Wierdwizard2587/ElectricGuitarMK1/Progress Photos/Design Phase/IMG_8852.JPEG

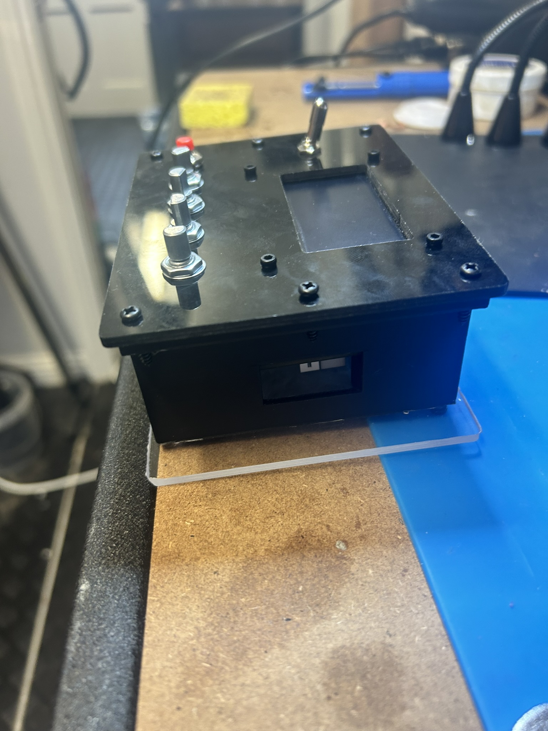
Progress Photos/Design Phase/IMG_8852.JPEG
