Wierdwizard2587/ElectricGuitarMK1/Progress Photos/Design Phase/IMG_9136.JPEG

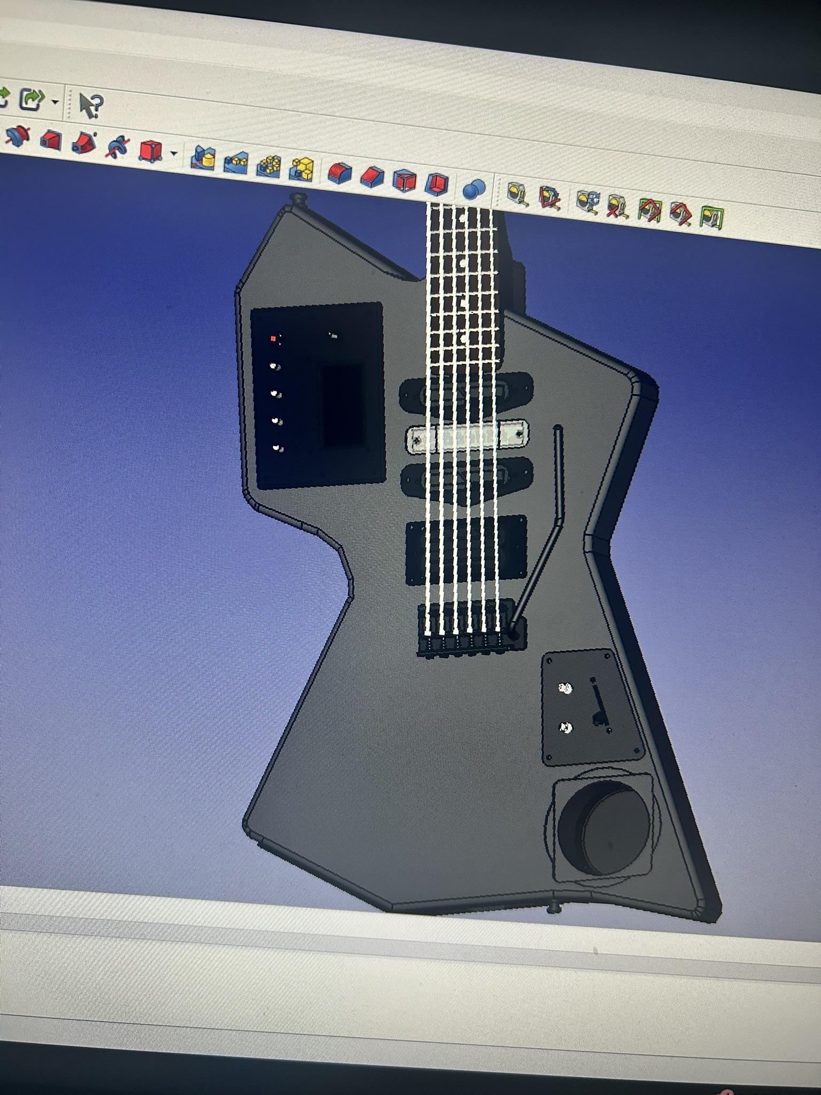
Progress Photos/Design Phase/IMG_9136.JPEG
