Wierdwizard2587/ElectricGuitarMK1/Progress Photos/Design Phase/IMG_9137.JPEG

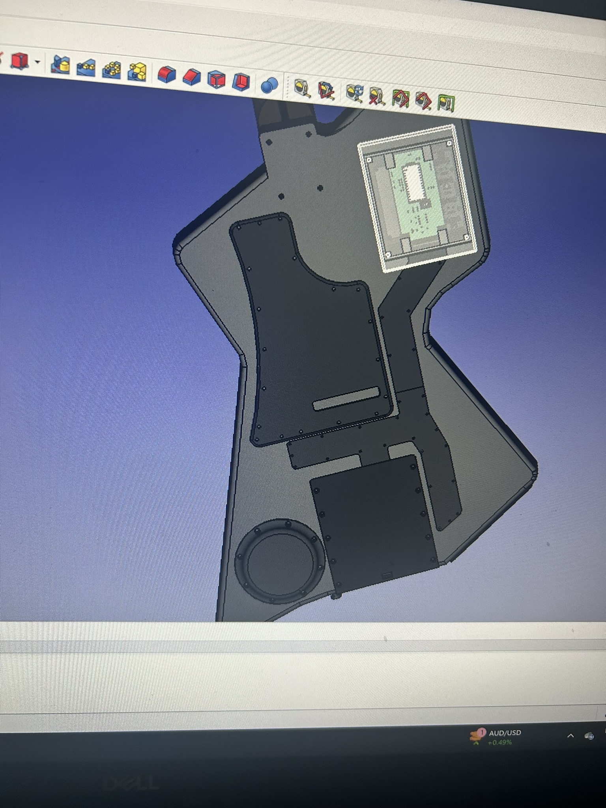
Progress Photos/Design Phase/IMG_9137.JPEG
