Wierdwizard2587/ElectricGuitarMK1/Progress Photos/Embedded Electronics/IMG_9527.jpg

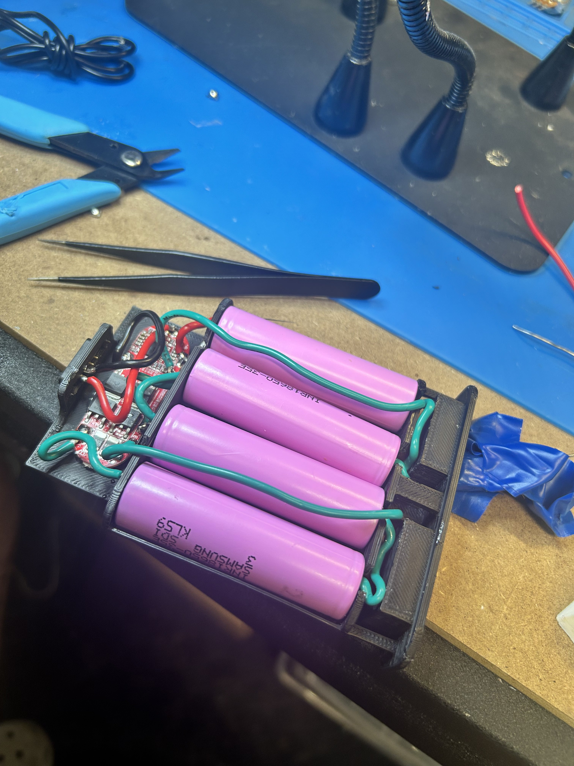
Progress Photos/Embedded Electronics/IMG_9527.jpg
