Wierdwizard2587/ElectricGuitarMK1/Progress Photos/Finished Product/IMG_9553.JPEG

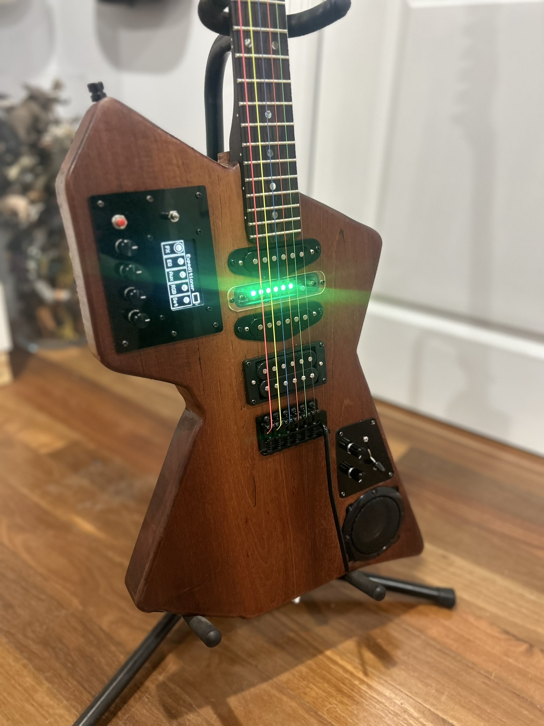
Progress Photos/Finished Product/IMG_9553.JPEG
