Wierdwizard2587/ElectricGuitarMK1/Progress Photos/Finished Product/IMG_9555.JPEG

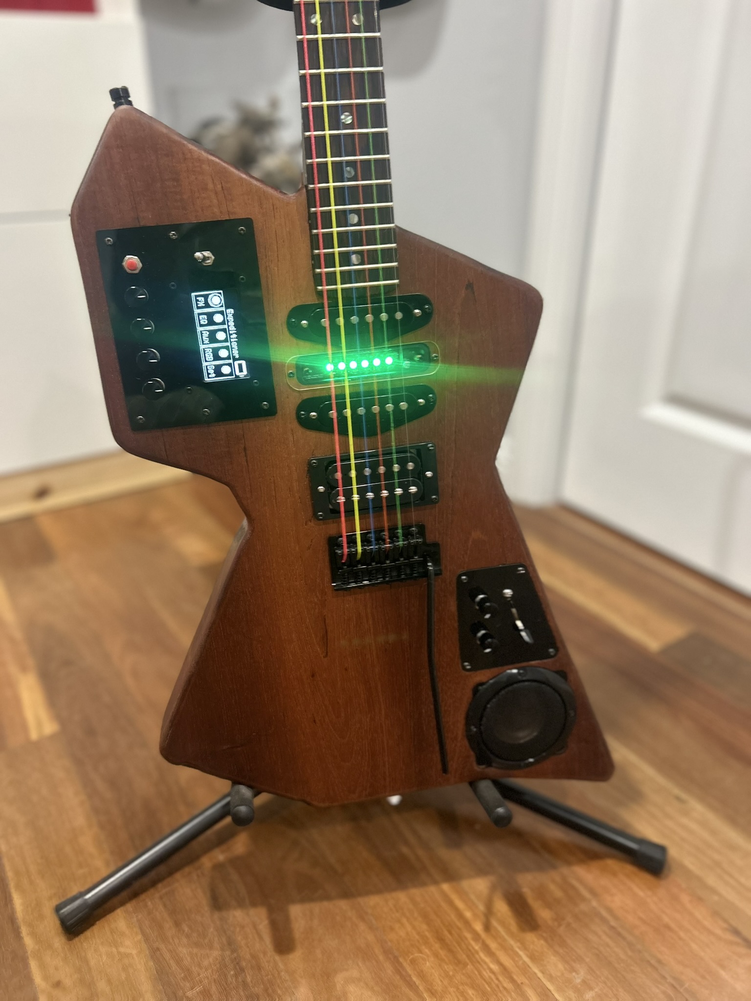
Progress Photos/Finished Product/IMG_9555.JPEG
