Wierdwizard2587/ElectricGuitarMK1/Progress Photos/Finished Product/IMG_9557.JPEG

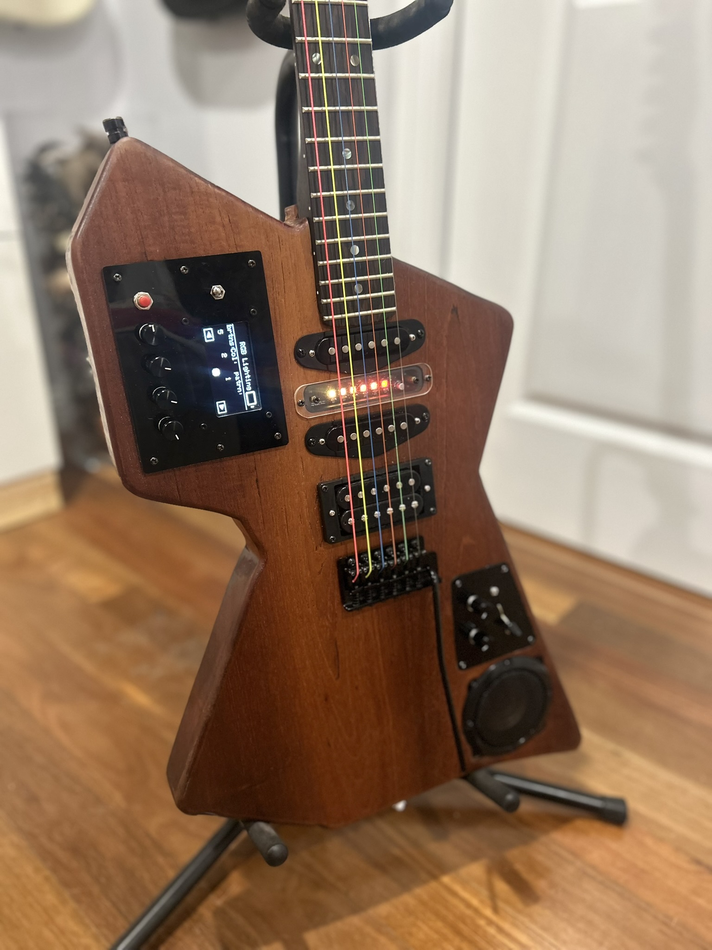
Progress Photos/Finished Product/IMG_9557.JPEG
