Wierdwizard2587/ElectricGuitarMK1/Progress Photos/MK 0 attempt/IMG_7361.JPEG

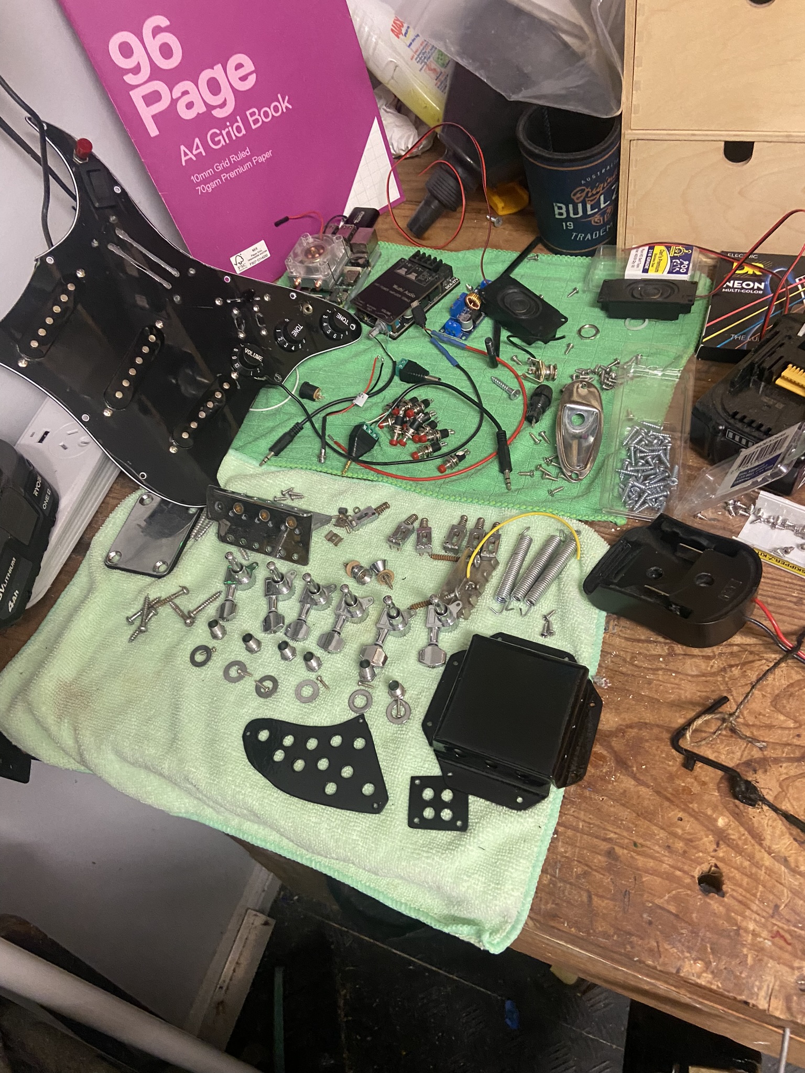
Progress Photos/MK 0 attempt/IMG_7361.JPEG
