Wierdwizard2587/ElectricGuitarMK1/Progress Photos/MK 0 attempt/IMG_7546.JPEG

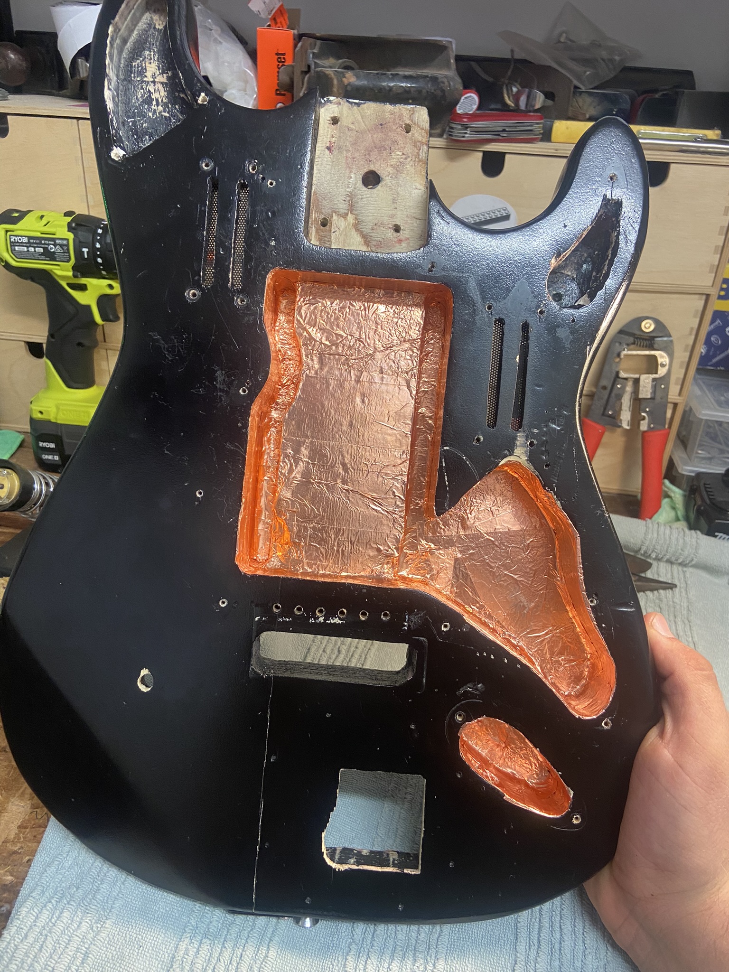
Progress Photos/MK 0 attempt/IMG_7546.JPEG
