Wierdwizard2587/ElectricGuitarMK1/Progress Photos/Skills Learnt/IMG_7960.JPEG

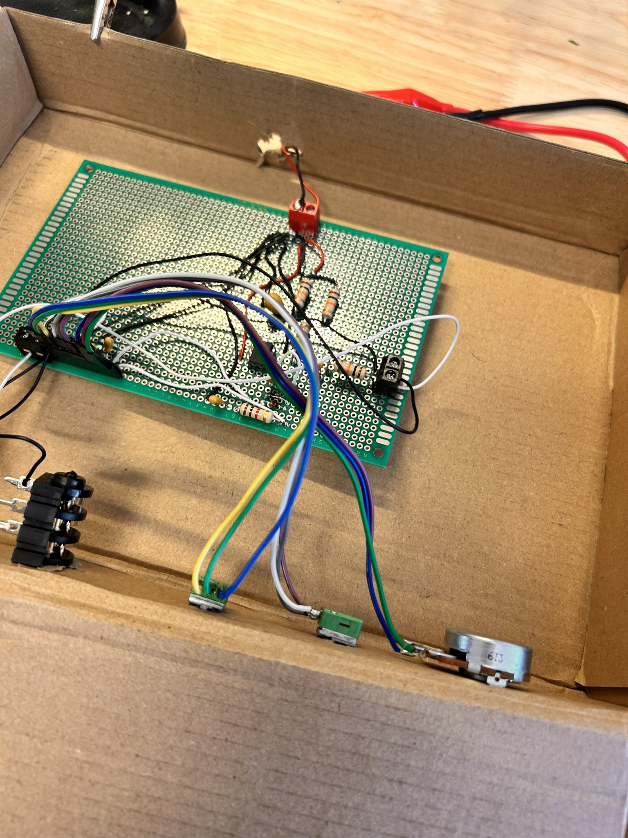
Progress Photos/Skills Learnt/IMG_7960.JPEG
