Wierdwizard2587/ElectricGuitarMK1/Progress Photos/Skills Learnt/IMG_7990.JPEG

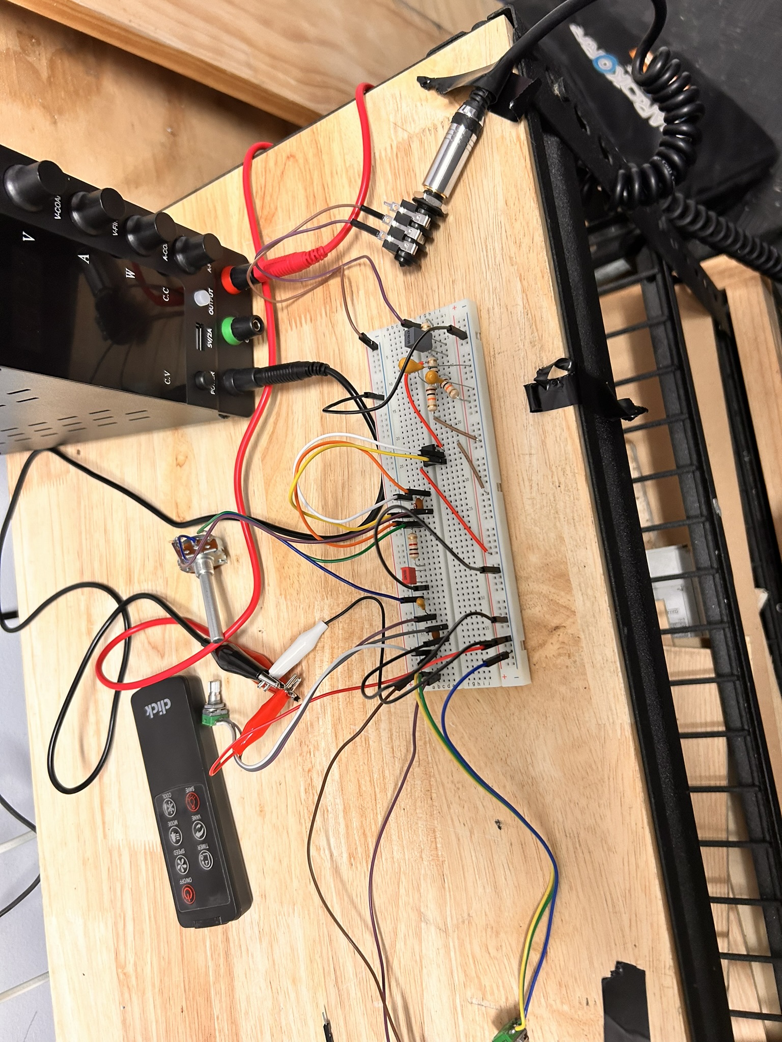
Progress Photos/Skills Learnt/IMG_7990.JPEG
