Wierdwizard2587/ElectricGuitarMK1/Progress Photos/Skills Learnt/IMG_8116.JPEG

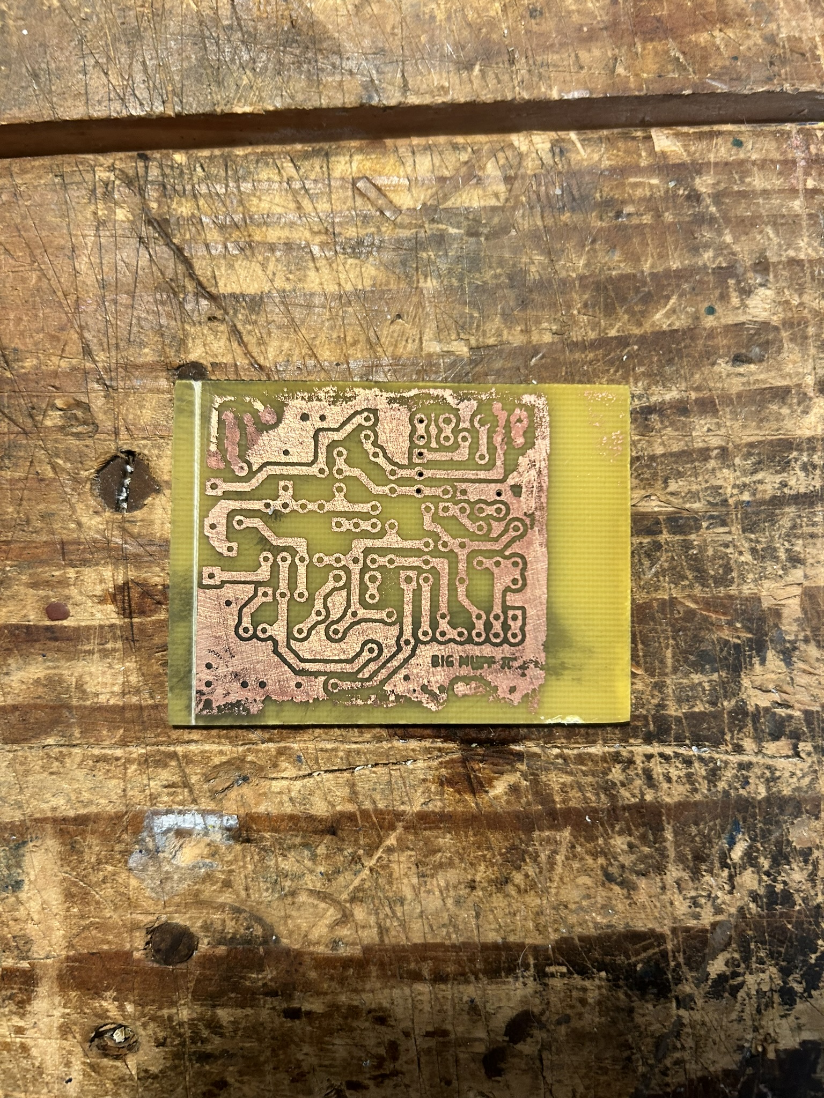
Progress Photos/Skills Learnt/IMG_8116.JPEG
