Wierdwizard2587/ElectricGuitarMK1/Progress Photos/Skills Learnt/IMG_8142.JPEG

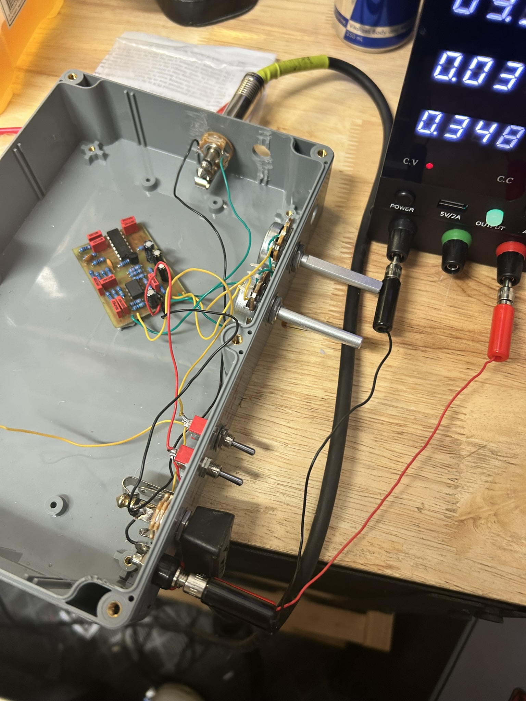
Progress Photos/Skills Learnt/IMG_8142.JPEG
