Wierdwizard2587/ElectricGuitarMK1/Progress Photos/Skills Learnt/IMG_8186.JPEG

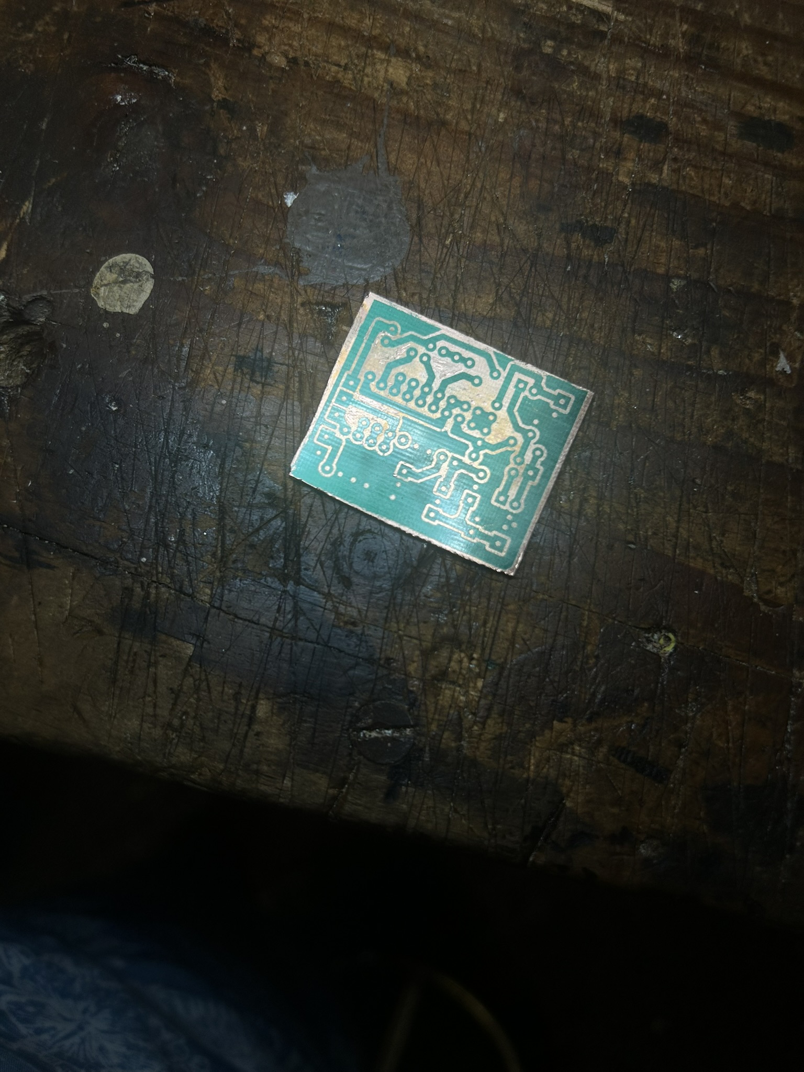
Progress Photos/Skills Learnt/IMG_8186.JPEG
