Wierdwizard2587/ElectricGuitarMK1/Progress Photos/Woodworking/IMG_9257.JPEG

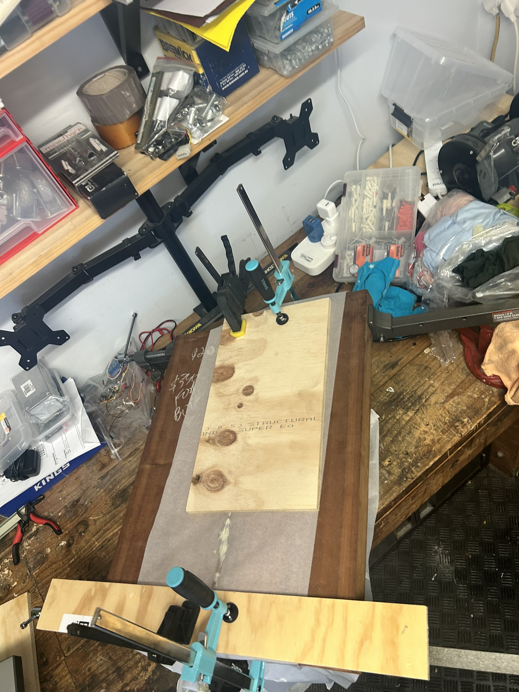
Progress Photos/Woodworking/IMG_9257.JPEG
