Wierdwizard2587/ElectricGuitarMK1/Progress Photos/Woodworking/IMG_9268.JPEG

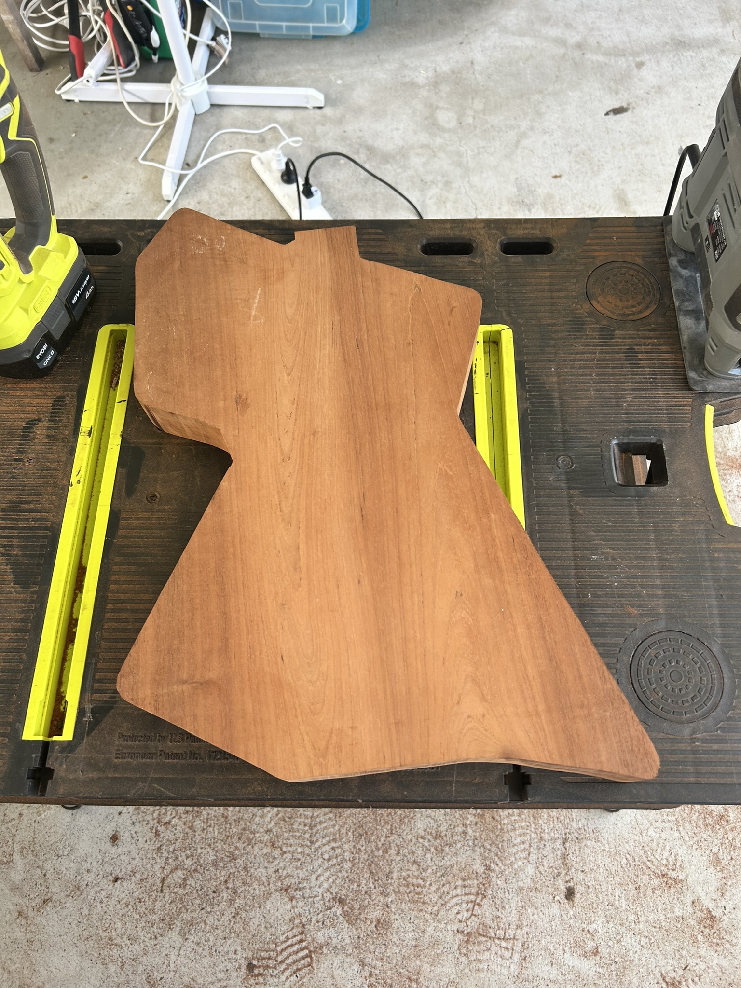
Progress Photos/Woodworking/IMG_9268.JPEG
