Wierdwizard2587/ElectricGuitarMK1/Progress Photos/Woodworking/IMG_9292.JPEG

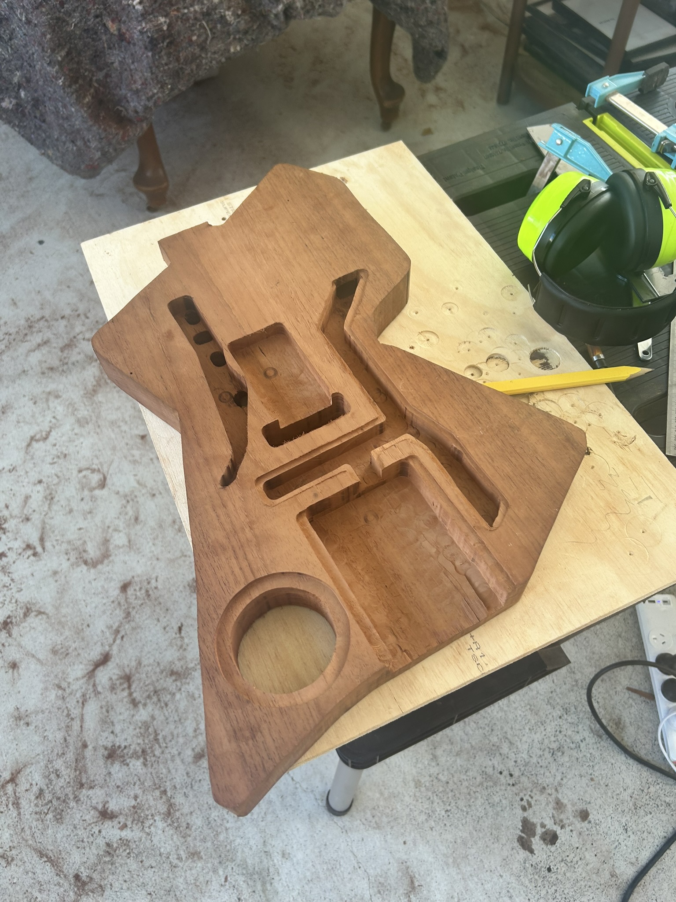
Progress Photos/Woodworking/IMG_9292.JPEG
