Wierdwizard2587/ElectricGuitarMK1/Progress Photos/Woodworking/IMG_9326.JPEG

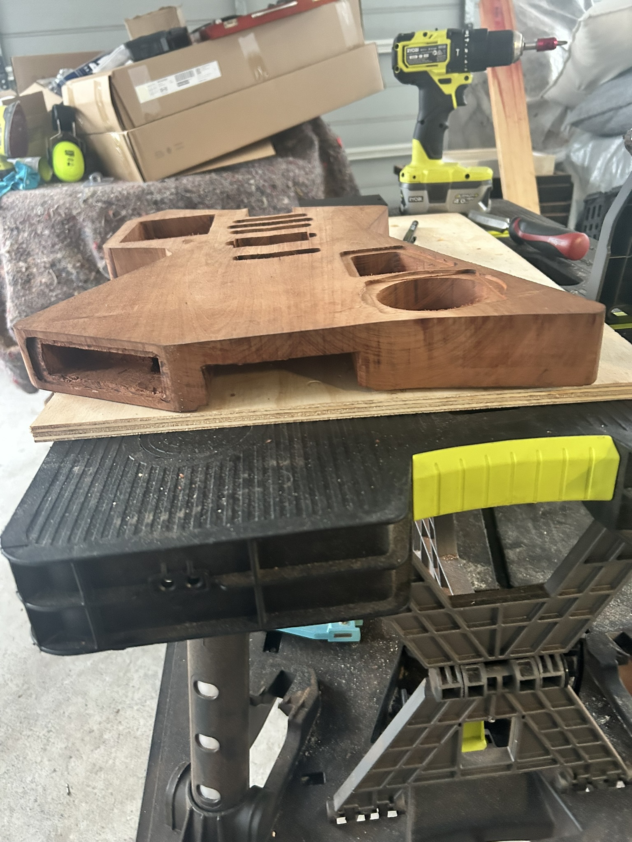
Progress Photos/Woodworking/IMG_9326.JPEG
