Wierdwizard2587/ElectricGuitarMK1/Progress Photos/Woodworking/IMG_9331.JPEG

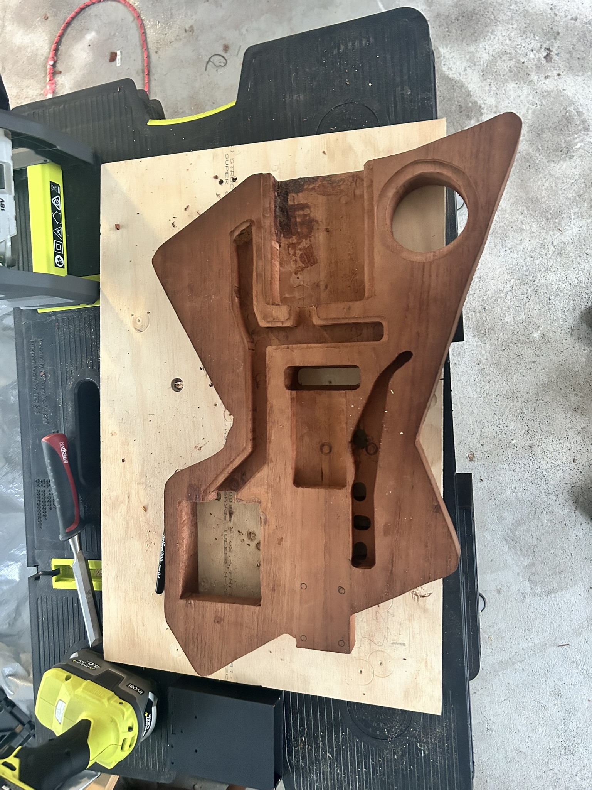
Progress Photos/Woodworking/IMG_9331.JPEG
