Wierdwizard2587/ElectricGuitarMK1/Progress Photos/Woodworking/IMG_9341.JPEG

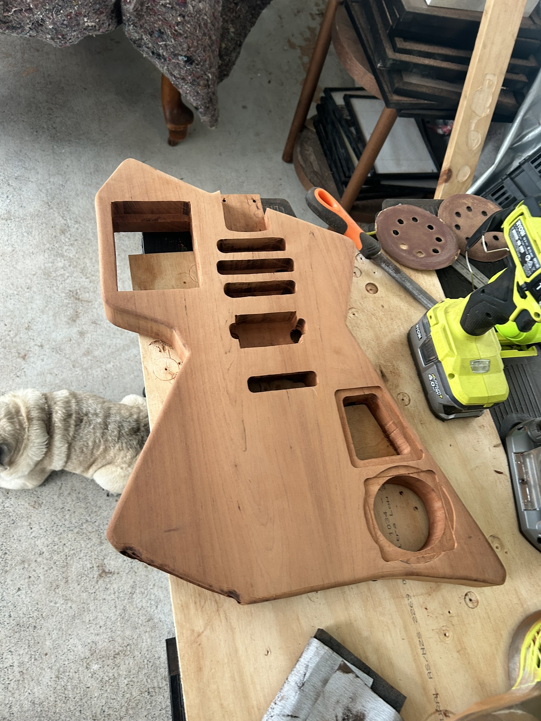
Progress Photos/Woodworking/IMG_9341.JPEG
