Wierdwizard2587/ElectricGuitarMK1/Progress Photos/Woodworking/IMG_9385.JPEG

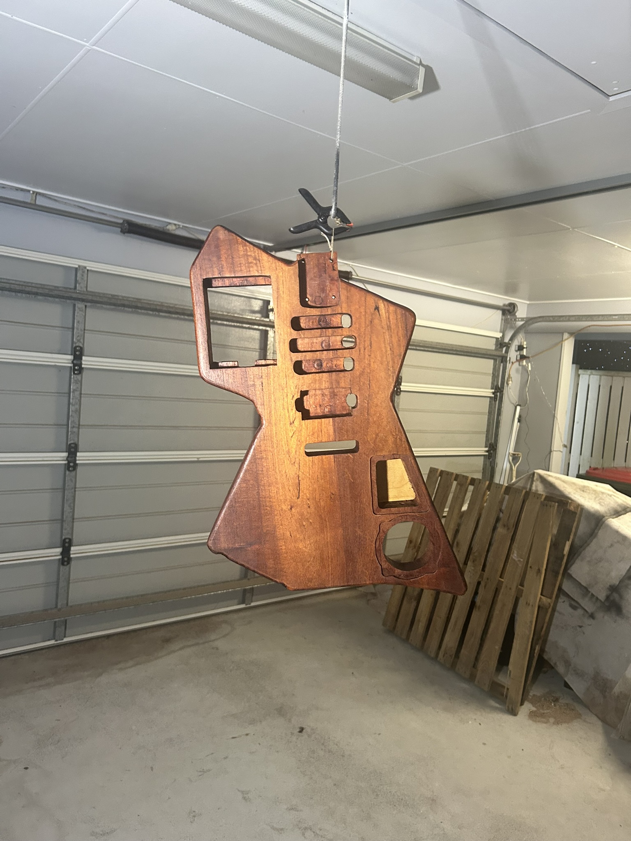
Progress Photos/Woodworking/IMG_9385.JPEG
