Wierdwizard2587/ElectricGuitarMK1/Research and Development/BMS/awg wire chart.webp

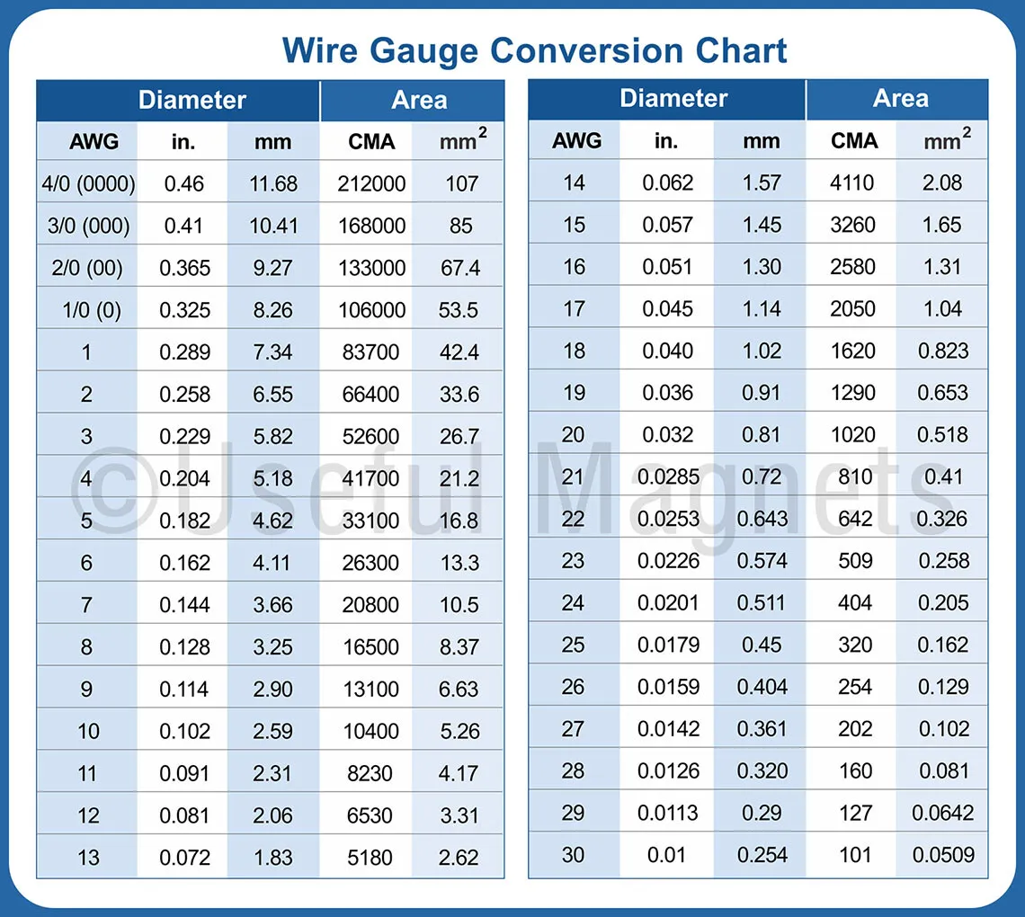
Research and Development/BMS/awg wire chart.webp
