Wierdwizard2587/ElectricGuitarMK1/Research and Development/BMS/Dimensions/Batt-Conn-magnetic-4p-Schem-Sheet.webp

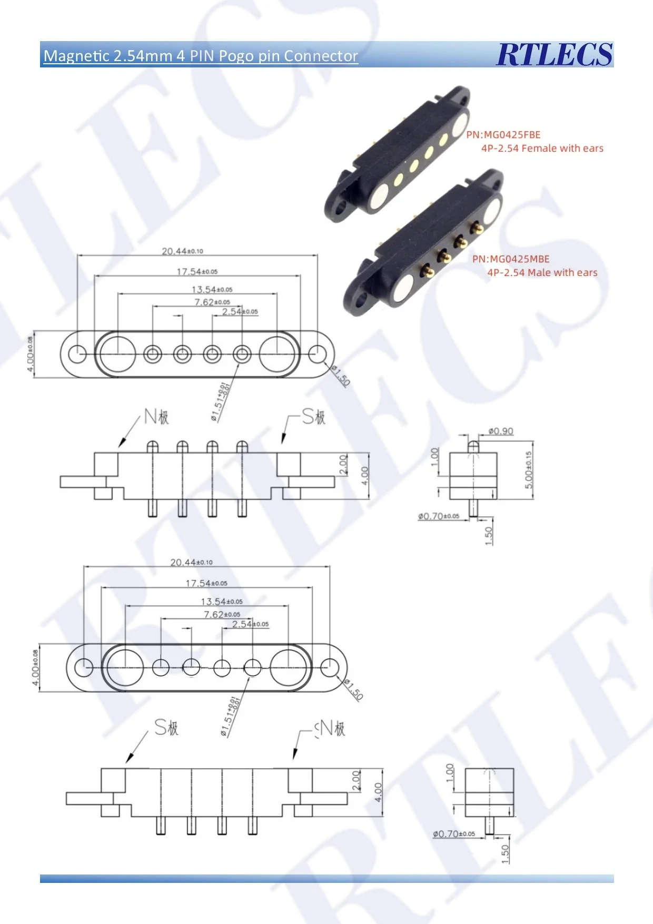
Research and Development/BMS/Dimensions/Batt-Conn-magnetic-4p-Schem-Sheet.webp
