Wierdwizard2587/ElectricGuitarMK1/Research and Development/BMS/Dimensions/battery spring terminal male 4pin dimensions.webp

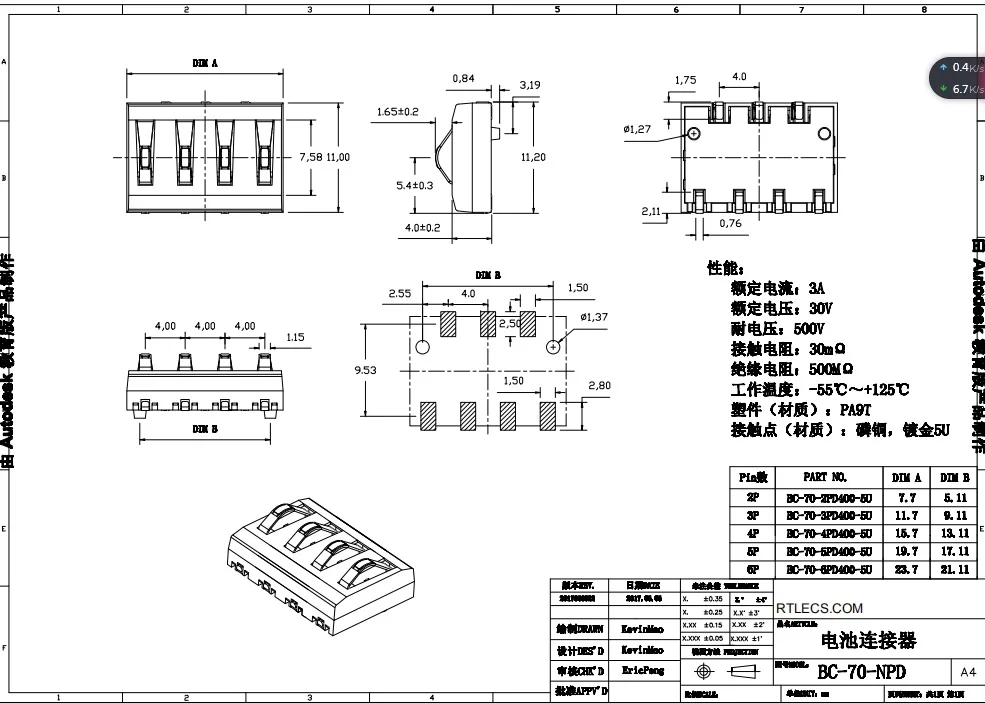
Research and Development/BMS/Dimensions/battery spring terminal male 4pin dimensions.webp
