Wierdwizard2587/ElectricGuitarMK1/Research and Development/BMS/Dimensions/battery terminal femal 4 pin dimensions.webp

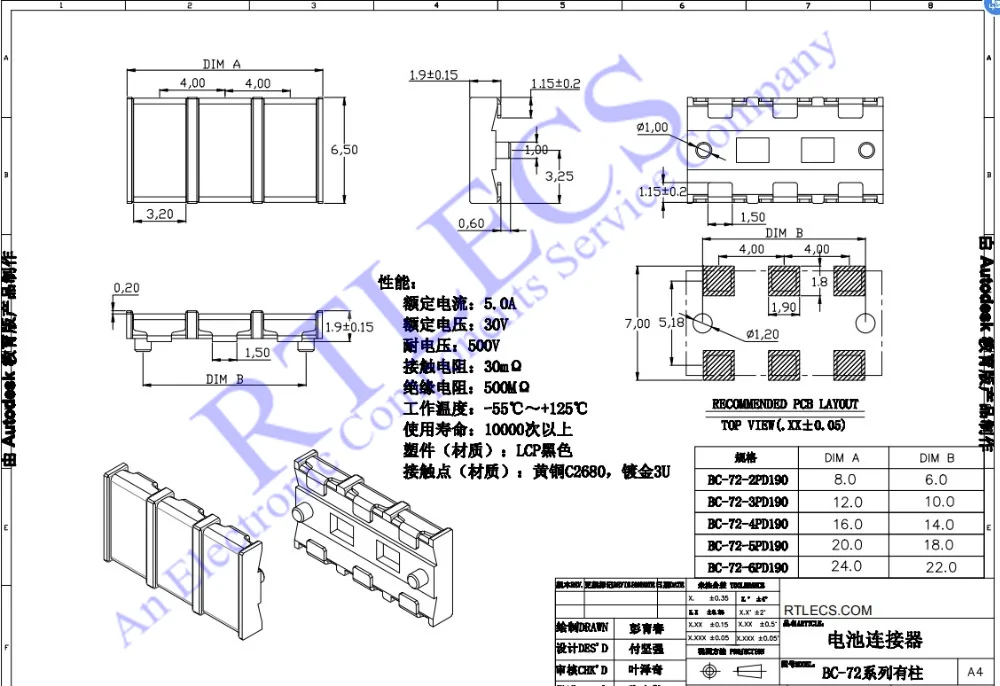
Research and Development/BMS/Dimensions/battery terminal femal 4 pin dimensions.webp
