Wierdwizard2587/ElectricGuitarMK1/Research and Development/BMS/Dimensions/smt battery holders dimensions.png

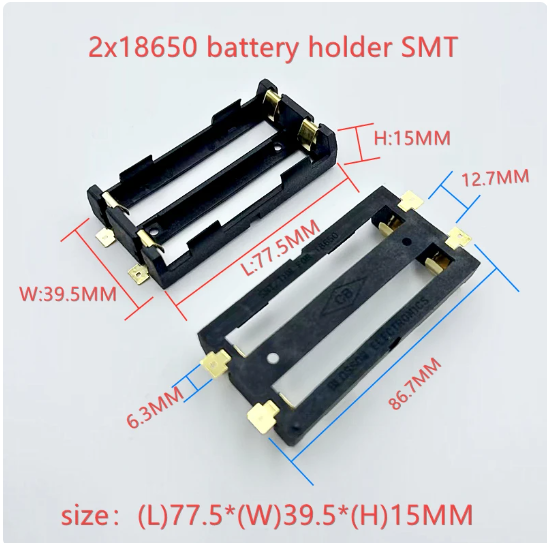
Research and Development/BMS/Dimensions/smt battery holders dimensions.png
