Wierdwizard2587/ElectricGuitarMK1/Research and Development/BMS/Docs/bms board battery and input config .png

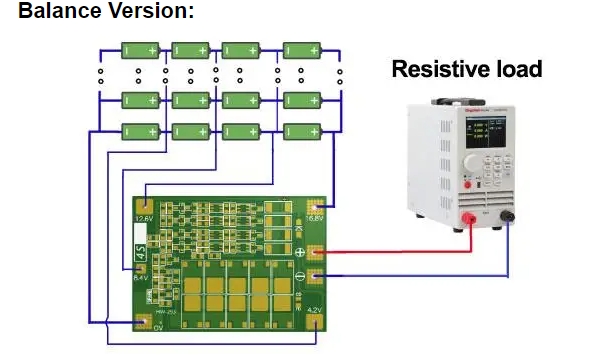
Research and Development/BMS/Docs/bms board battery and input config .png
