Wierdwizard2587/ElectricGuitarMK1/Research and Development/BMS/PCB Design/3.0 BMS/V3.2/bmsboardlayoutv1.png

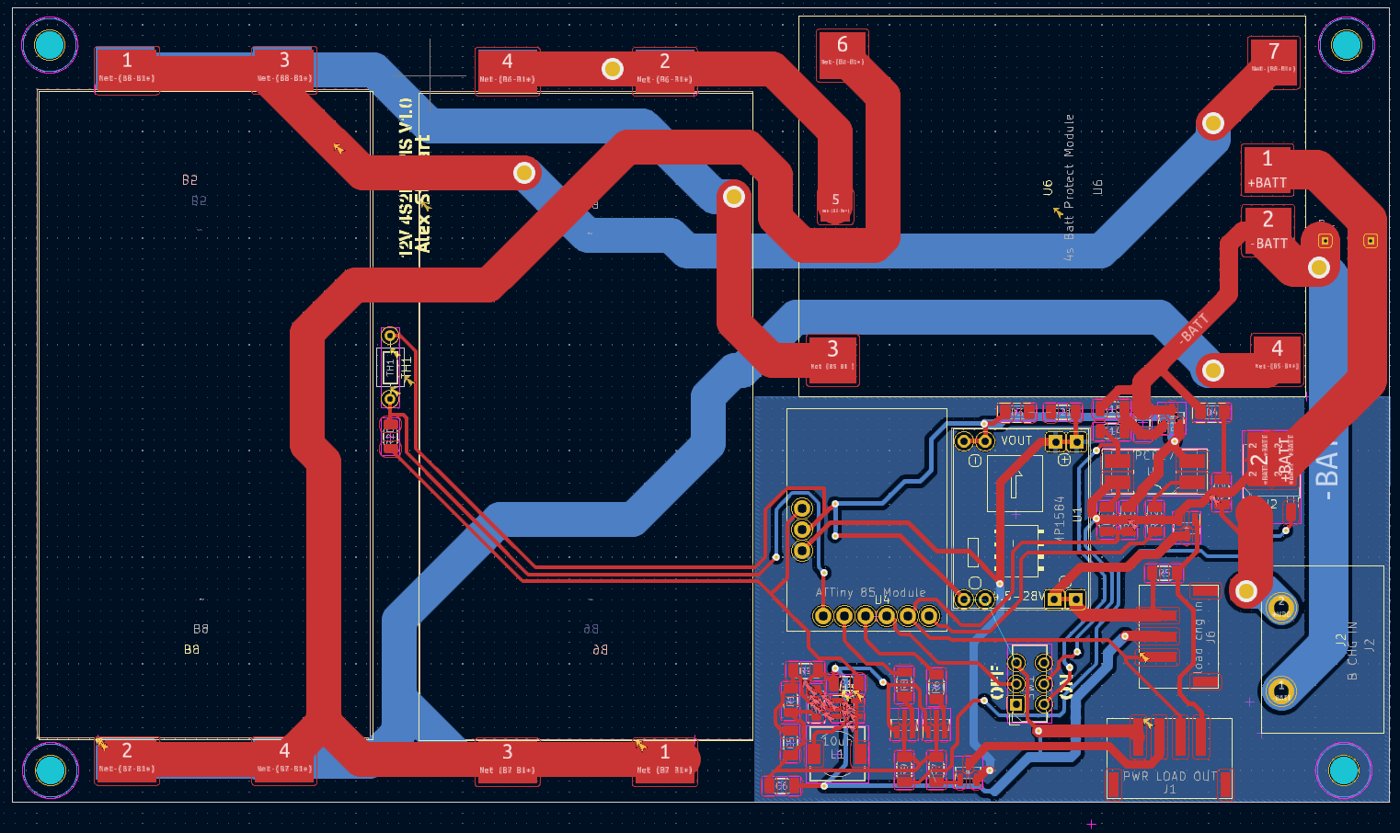
Research and Development/BMS/PCB Design/3.0 BMS/V3.2/bmsboardlayoutv1.png
