Wierdwizard2587/ElectricGuitarMK1/Research and Development/Body design/3d models and docs/spst button/button render.png

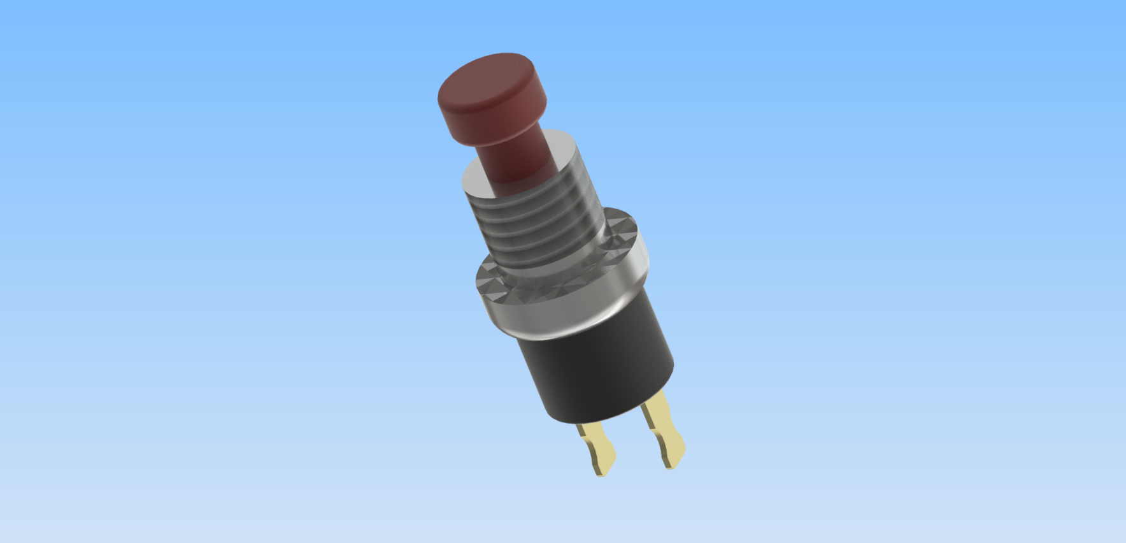
Research and Development/Body design/3d models and docs/spst button/button render.png
