Wierdwizard2587/ElectricGuitarMK1/Research and Development/FX Circuits/ProCo Rat/procoratpcblayout.png

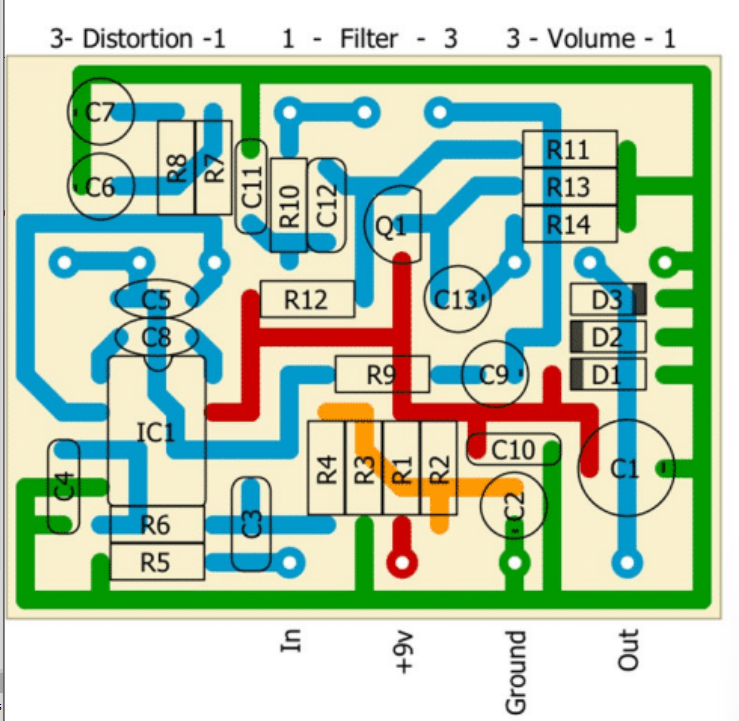
Research and Development/FX Circuits/ProCo Rat/procoratpcblayout.png
