Wierdwizard2587/ElectricGuitarMK1/Research and Development/Interface Section/AFPI/Enclosure Design/3D Models/quad Rotary Encoder Board/Adafruit 5752.png

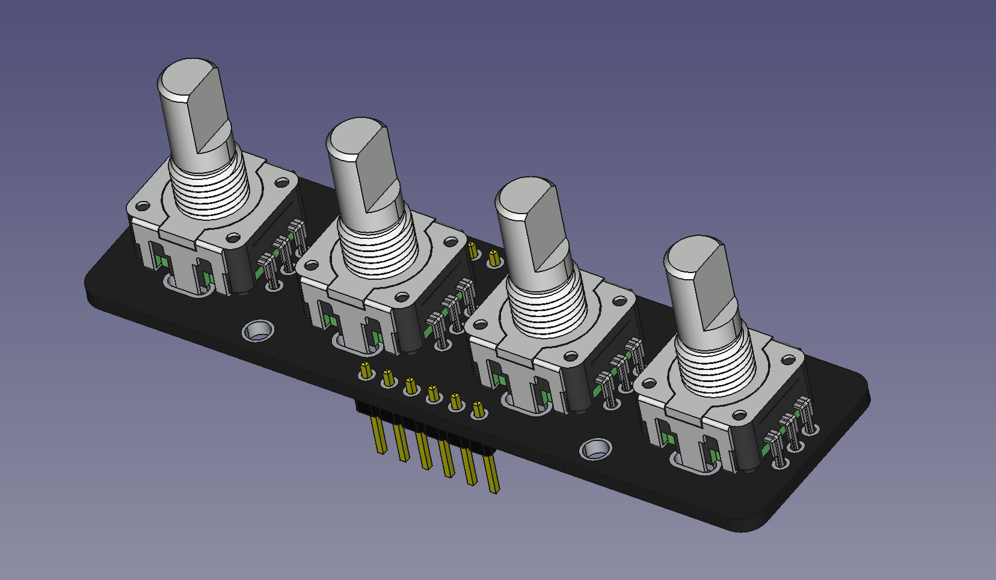
Research and Development/Interface Section/AFPI/Enclosure Design/3D Models/quad Rotary Encoder Board/Adafruit 5752.png
