Wierdwizard2587/ElectricGuitarMK1/Research and Development/Interface Section/AFPI/Enclosure Design/AFPI Final Documents/Enclosure Images/right view.png

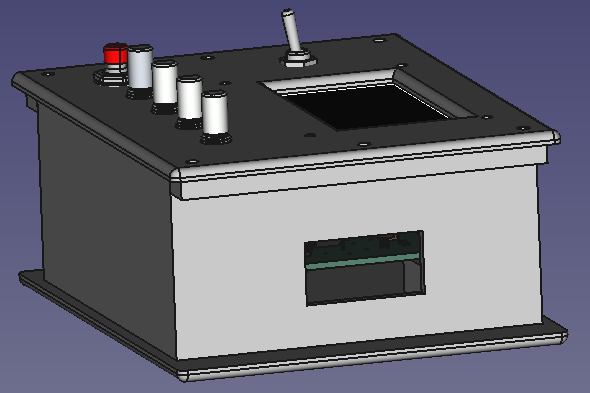
Research and Development/Interface Section/AFPI/Enclosure Design/AFPI Final Documents/Enclosure Images/right view.png
