Wierdwizard2587/ElectricGuitarMK1/Research and Development/Interface Section/compass.jpg

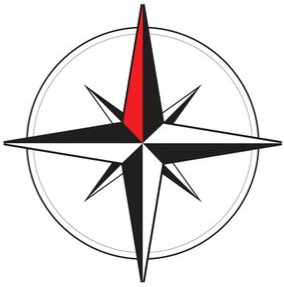
Research and Development/Interface Section/compass.jpg
