Wierdwizard2587/ElectricGuitarMK1/Research and Development/Body design/body and neck scaled 3d models/Expeditioner Model-Body Mk 1.stl

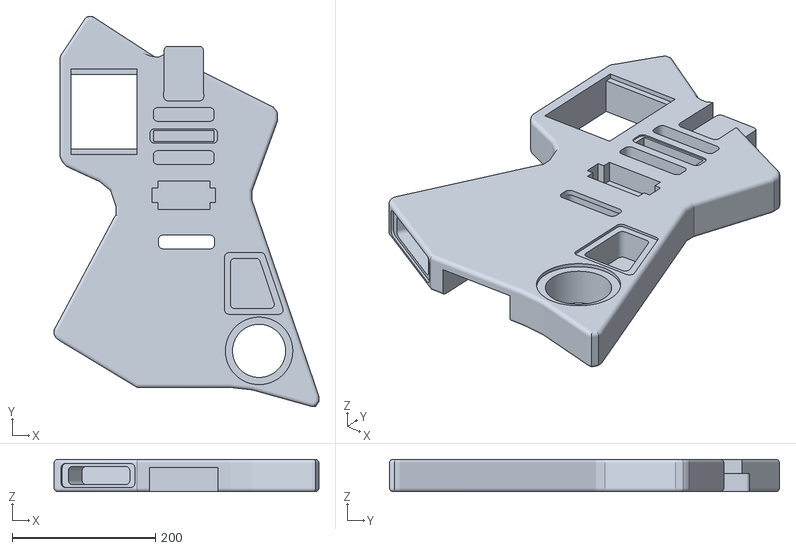
[picture p156: CAD file, 2025-05-16]
Research and Development/Body design/body and neck scaled 3d models/Expeditioner Model-Body Mk 1.stl
369.2 x 543.6 x 45.0
