Wierdwizard2587/ElectricGuitarMK1/Research and Development/Body design/body Components Tool Paths/Back plate 1 tool path.FCStd

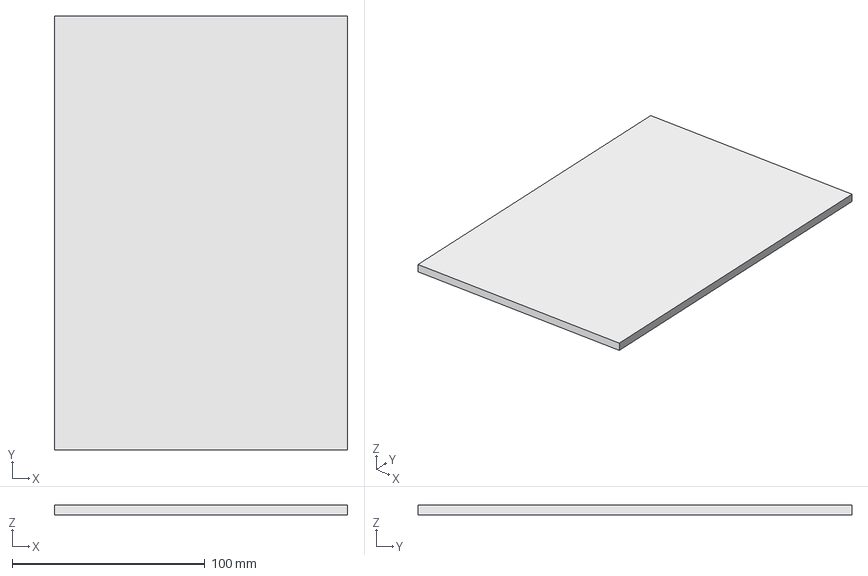
[picture p157: CAD file, 2025-05-16]
Research and Development/Body design/body Components Tool Paths/Back plate 1 tool path.FCStd
152.0 x 225.0 x 5.00 mm
Model-Back Plate 1
Stock
