Wierdwizard2587/ElectricGuitarMK1/Research and Development/Body design/body Components Tool Paths/Back Plate 1/Back Plate 1 tool path.FCStd

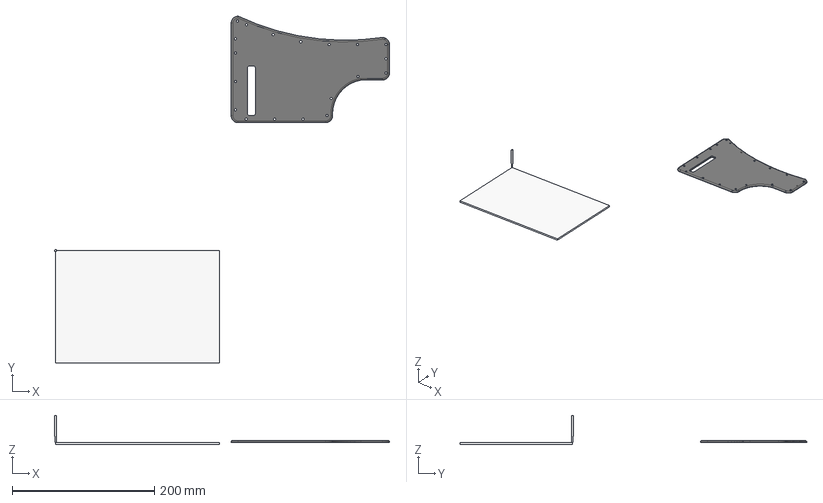
[picture p158: CAD file, 2025-05-16]
Research and Development/Body design/body Components Tool Paths/Back Plate 1/Back Plate 1 tool path.FCStd
471.5 x 488.0 x 41.1 mm
Back Plate 1
Stock001
2.3mm_endmill001
