Wierdwizard2587/ElectricGuitarMK1/Research and Development/Body design/body Components Tool Paths/Control Cavity Plate/Control Cavity Tool Path.FCStd

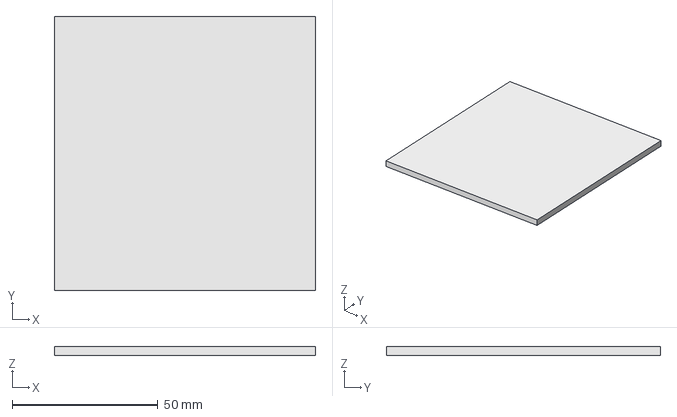
[picture p159: CAD file, 2025-05-16]
Research and Development/Body design/body Components Tool Paths/Control Cavity Plate/Control Cavity Tool Path.FCStd
89.6 x 94.0 x 3.00 mm
