Wierdwizard2587/ElectricGuitarMK1/Research and Development/Body design/Expeditioner Model-Rear Speaker Cover .stl

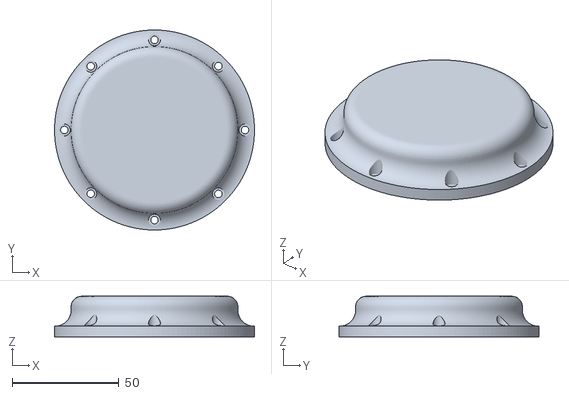
[picture p161: CAD file, 2025-05-16]
Research and Development/Body design/Expeditioner Model-Rear Speaker Cover .stl
93.5 x 93.5 x 19.0
