Wierdwizard2587/ElectricGuitarMK1/Research and Development/FX Circuits/Big muff portion/Big muff portion test download for free cad.step

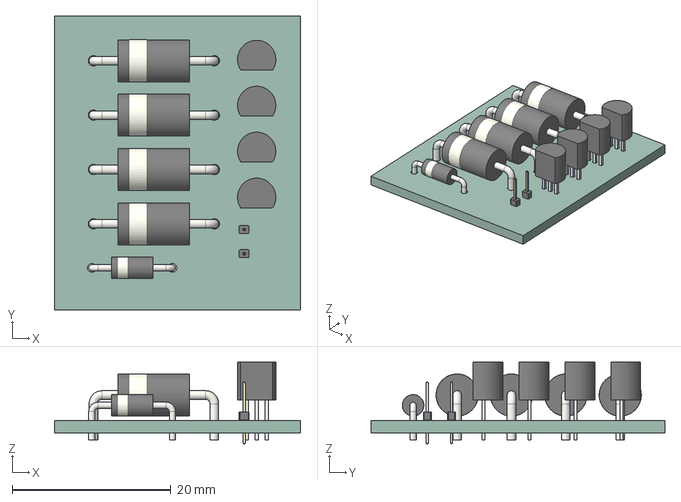
[picture p162: CAD file, 2024-06-03]
Research and Development/FX Circuits/Big muff portion/Big muff portion test download for free cad.step
31.0 x 37.0 x 10.3 mm
_autosave-Big muff portion PCB
