Wierdwizard2587/ElectricGuitarMK1/Research and Development/Interface Section/AFPI/Enclosure Design/3D Models/2.42 inch OLED Display_Own Design/2.42 OLED Display.step

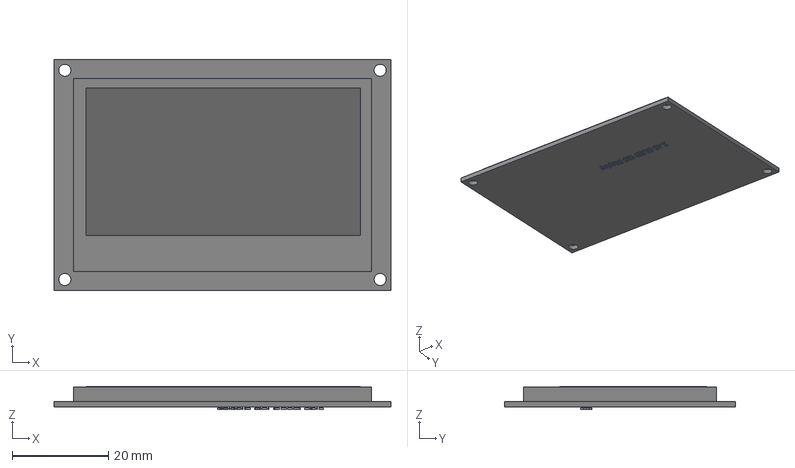
[picture p163: CAD file, 2024-08-15]
Research and Development/Interface Section/AFPI/Enclosure Design/3D Models/2.42 inch OLED Display_Own Design/2.42 OLED Display.step
70.0 x 48.0 x 4.78 mm
Hole
