Wierdwizard2587/ElectricGuitarMK1/Research and Development/Interface Section/AFPI/Enclosure Design/3D Models/SPST Home Switch/Pushbutton v16.step

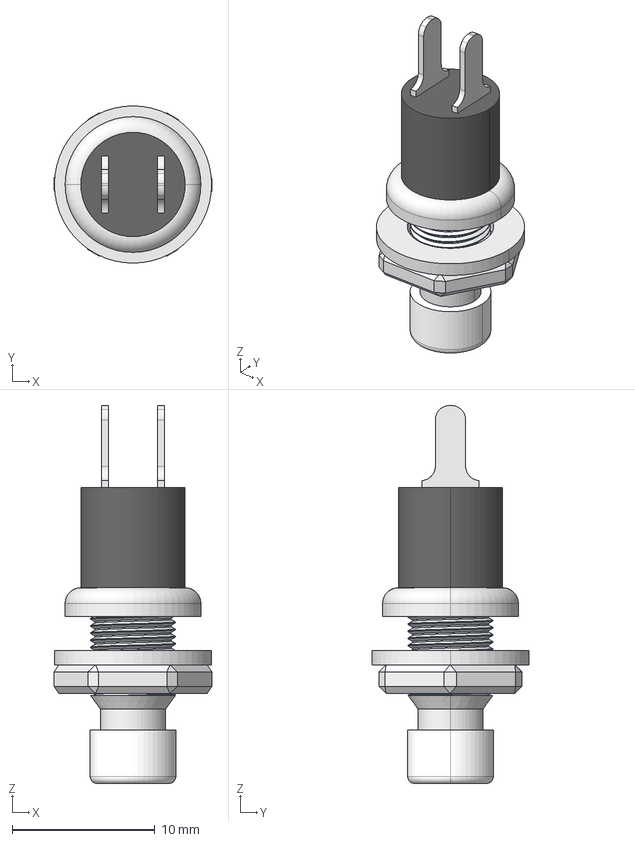
[picture p164: CAD file, 2024-08-15]
Research and Development/Interface Section/AFPI/Enclosure Design/3D Models/SPST Home Switch/Pushbutton v16.step
11.1 x 11.0 x 26.4 mm
Washer
Cap
Metal Body
Plastic Body
Contact 1
Contact 2
Nut
