Wierdwizard2587/ElectricGuitarMK1/Research and Development/Interface Section/AFPI/Enclosure Design/3D Models/SPST Power Switch/6mm SPDT Mini Toggle Switch.step

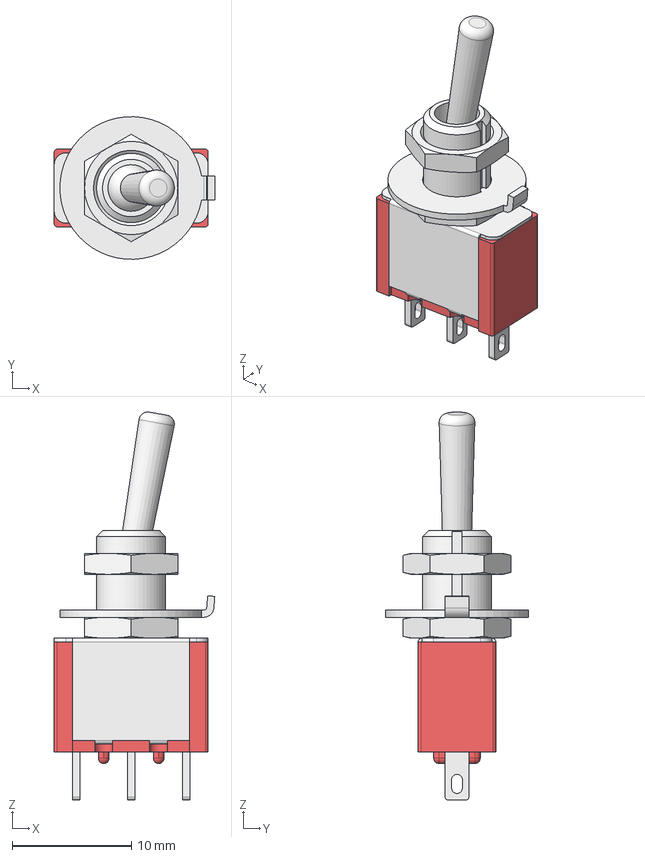
[picture p165: CAD file, 2024-08-15]
Research and Development/Interface Section/AFPI/Enclosure Design/3D Models/SPST Power Switch/6mm SPDT Mini Toggle Switch.step
13.4 x 11.9 x 32.5 mm
