Wierdwizard2587/ElectricGuitarMK1/Research and Development/Interface Section/AFPI/Enclosure Design/Acrylic Plating Gcode/AFPI Enclosure Model-EnclosureTop Enclosure Plate.step

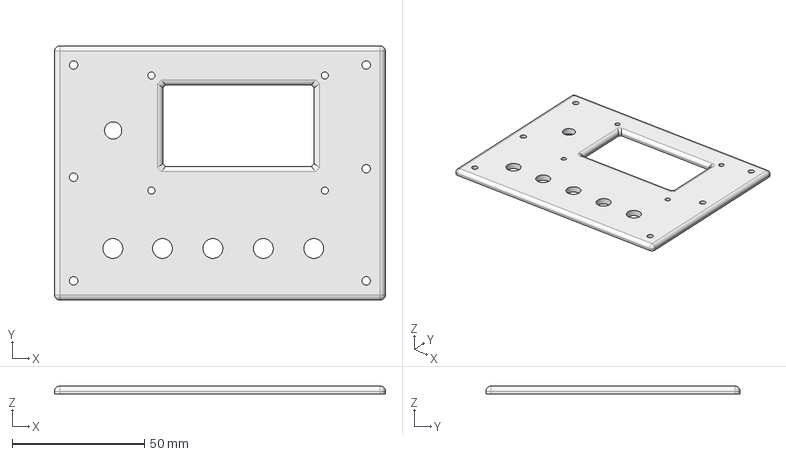
[picture p166: CAD file, 2024-08-15]
Research and Development/Interface Section/AFPI/Enclosure Design/Acrylic Plating Gcode/AFPI Enclosure Model-EnclosureTop Enclosure Plate.step
125.0 x 96.0 x 3.00 mm
