Wierdwizard2587/ElectricGuitarMK1/Research and Development/Interface Section/AFPI/Enclosure Design/AFPI Final Documents/AFPI Enclosure Model-Enclosure Centre Exterior .stl

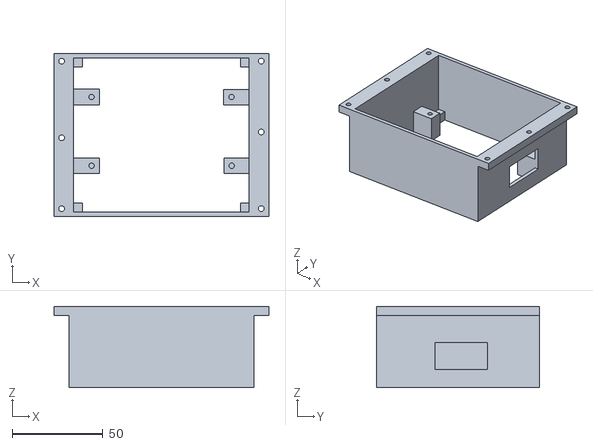
[picture p167: CAD file, 2024-08-15]
Research and Development/Interface Section/AFPI/Enclosure Design/AFPI Final Documents/AFPI Enclosure Model-Enclosure Centre Exterior .stl
118.8 x 90.1 x 45.0
