Wierdwizard2587/ElectricGuitarMK1/Research and Development/Interface Section/AFPI/Enclosure Design/Bottom Plate CNC Job.FCStd

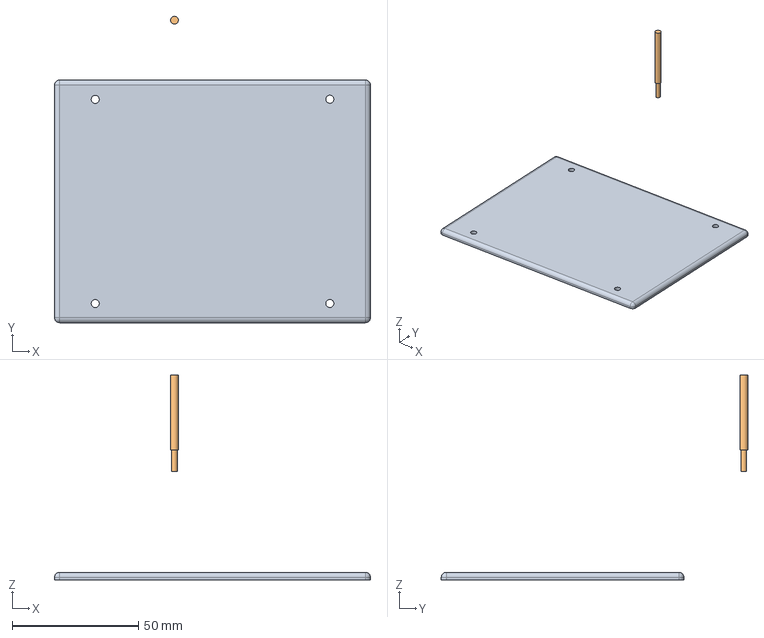
[picture p168: CAD file, 2025-05-16]
Research and Development/Interface Section/AFPI/Enclosure Design/Bottom Plate CNC Job.FCStd
125.0 x 121.2 x 81.0 mm
Bottom Plate
2.3mm_endmill
