Wierdwizard2587/ElectricGuitarMK1/Research and Development/Interface Section/AFPI/Enclosure Design/Saves/AFPI Enclosure Model save_with face plate.FCStd

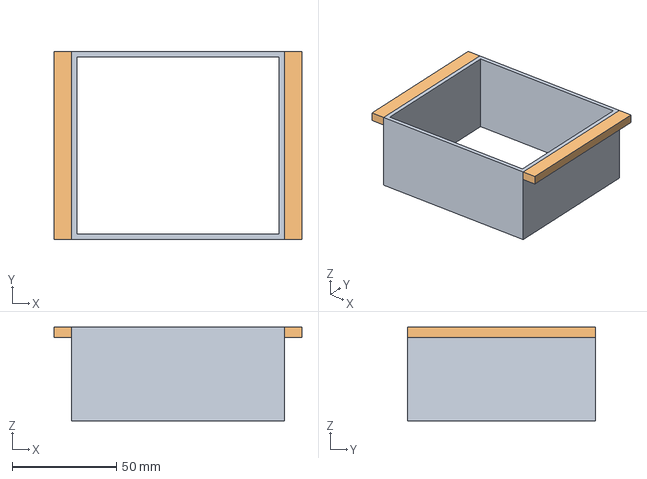
[picture p169: CAD file, 2024-08-15]
Research and Development/Interface Section/AFPI/Enclosure Design/Saves/AFPI Enclosure Model save_with face plate.FCStd
119.0 x 90.0 x 45.0 mm
Walls
exterior Mounting Lip
