Wierdwizard2587/ElectricGuitarMK1/Research and Development/Interface Section/IO Platw.FCStd

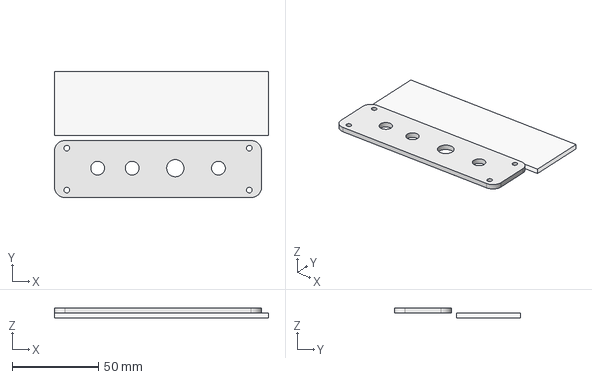
[picture p170: CAD file, 2025-05-16]
Research and Development/Interface Section/IO Platw.FCStd
124.0 x 73.0 x 6.00 mm
Stock
