Wierdwizard2587/ElectricGuitarMK1/Research and Development/Interface Section/RGB Lighting comps/RGB LED Mounting Board.step

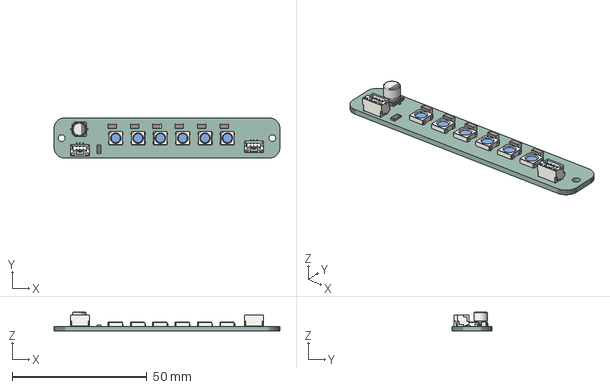
[picture p171: CAD file, 2025-05-16]
Research and Development/Interface Section/RGB Lighting comps/RGB LED Mounting Board.step
84.0 x 14.9 x 7.05 mm
RGB LED Mounting Board PCB
