Wierdwizard2587/ElectricGuitarMK1/Research and Development/Interface Section/RGB Lighting comps/RGB LED Mounting Board/light case test.stl

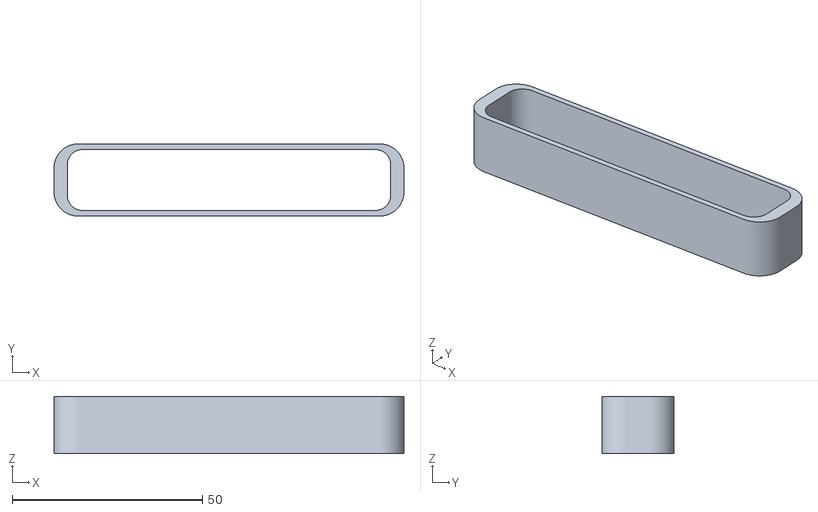
[picture p172: CAD file, 2025-05-16]
Research and Development/Interface Section/RGB Lighting comps/RGB LED Mounting Board/light case test.stl
92.0 x 19.0 x 15.0
