Wierdwizard2587/ElectricGuitarMK1/Research and Development/Storage Draw seperators/storage draw seperator 2.stl

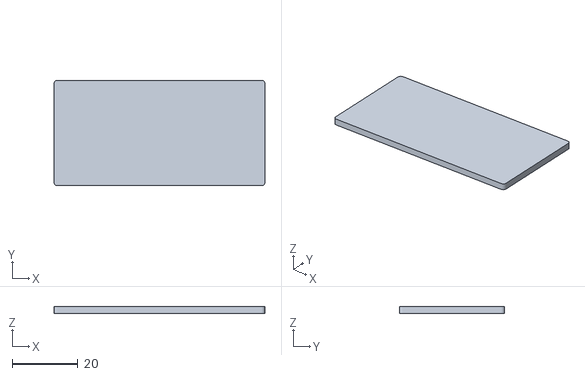
[picture p173: CAD file, 2024-06-03]
Research and Development/Storage Draw seperators/storage draw seperator 2.stl
64.0 x 32.0 x 2.00
