Wierdwizard2587/ElectricGuitarMK1/Research and Development/Tool Testing/heat insert test holes.stl

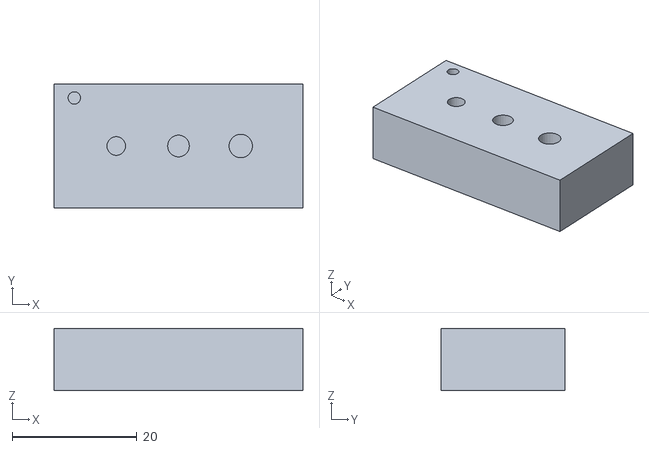
[picture p174: CAD file, 2024-06-03]
Research and Development/Tool Testing/heat insert test holes.stl
40.0 x 20.0 x 10.0
