Wierdwizard2587/ElectricGuitarMK1/Research and Development/BMS/enclosure modelling/Battery Cell Mount Designs - not-utilised-Anymore/Battery holder initial designing/battery mk 1.FCStd

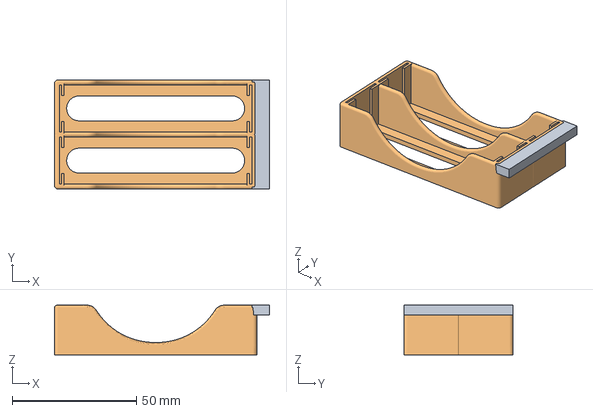
[picture p175: CAD file, 2024-06-03]
Research and Development/BMS/enclosure modelling/Battery Cell Mount Designs - not-utilised-Anymore/Battery holder initial designing/battery mk 1.FCStd
86.5 x 44.0 x 20.0 mm
screw pot
2_Batterie_2.0
