Wierdwizard2587/ElectricGuitarMK1/Research and Development/BMS/enclosure modelling/Battery Cell Mount Designs - not-utilised-Anymore/design attempt 1/design attempt 1.FCStd

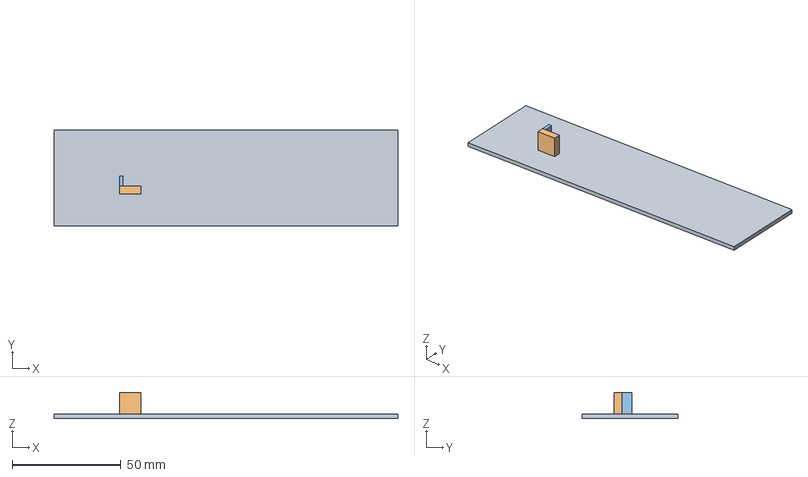
[picture p176: CAD file, 2024-06-03]
Research and Development/BMS/enclosure modelling/Battery Cell Mount Designs - not-utilised-Anymore/design attempt 1/design attempt 1.FCStd
158.0 x 44.0 x 12.0 mm
