Wierdwizard2587/ElectricGuitarMK1/Research and Development/BMS/enclosure modelling/battery power rocker switch head.FCStd

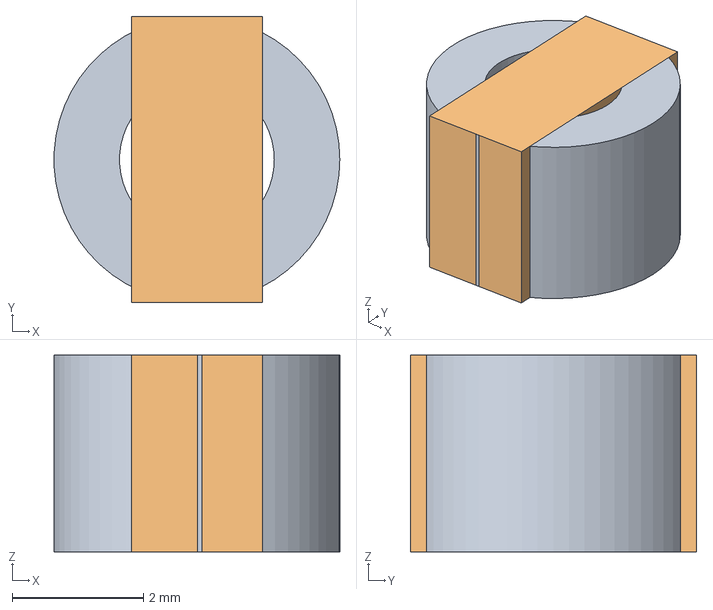
[picture p178: CAD file, 2024-06-17]
Research and Development/BMS/enclosure modelling/battery power rocker switch head.FCStd
4.36 x 4.36 x 3.00 mm
