Wierdwizard2587/ElectricGuitarMK1/Research and Development/BMS/FInal Battery Design/Final Battery Design.FCStd

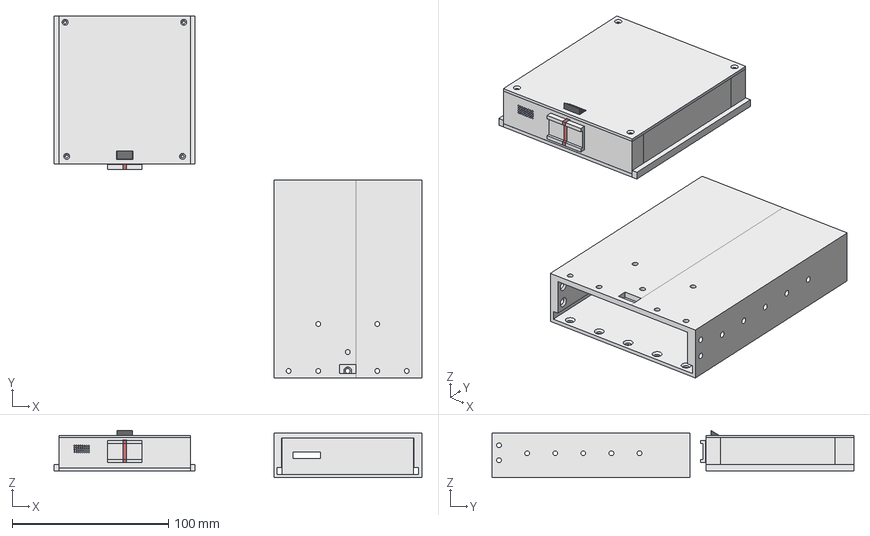
[picture p179: CAD file, 2025-05-16]
Research and Development/BMS/FInal Battery Design/Final Battery Design.FCStd
235.5 x 231.9 x 30.2 mm
BACK FLOOR
FRONT BODY
BACK LEFT INSERT MNT
FRONT FLOOR
FRONT LEFT INSERT MNT
FRONT RIGHT INSERT MNT
FRONT LOCK SLOT
BACK WALL
BACK RIGHT INSERT MNT
CELL ENDS SPRING HOLDERS
CELL DIVIDER WALLS
CELL MOUNT FLOOR
TOP PLATE BODY
SPRING CYLINDER
LOCK SLIDE HOOK
MAIN LOCKING HANDLE MNT
BASE HANDLE INSERT
PIN BASE
PIN LENGTH
cell 001
cell 002
cell 003
cell 004
exterior sleeve
