Wierdwizard2587/ElectricGuitarMK1/Research and Development/BMS/FInal Battery Design/Final Design V2/Battery V2-Battery V2Batt Component Insert.stl

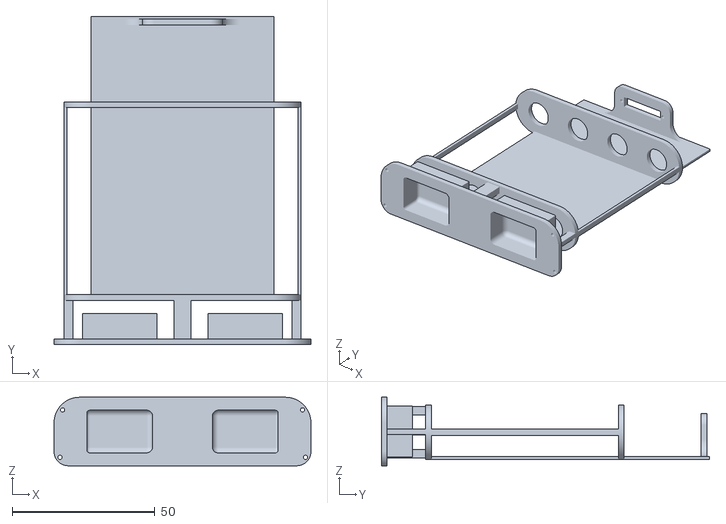
[picture p180: CAD file, 2025-05-16]
Research and Development/BMS/FInal Battery Design/Final Design V2/Battery V2-Battery V2Batt Component Insert.stl
90.0 x 115.0 x 24.0
