Wierdwizard2587/ElectricGuitarMK1/Research and Development/Body design/body Components Tool Paths/Back plate 2 TOol path.FCStd

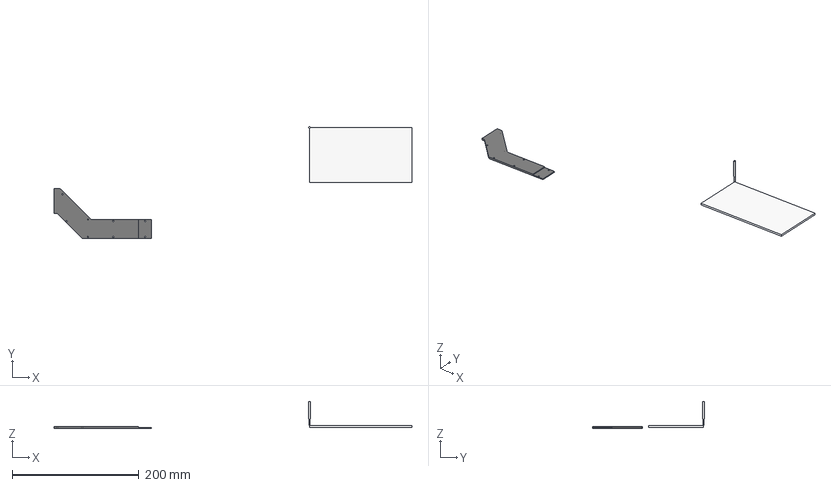
[picture p181: CAD file, 2025-05-16]
Research and Development/Body design/body Components Tool Paths/Back plate 2 TOol path.FCStd
564.0 x 176.5 x 43.0 mm
Back Plate 2
Stock
2mm_Endmill
