Wierdwizard2587/ElectricGuitarMK1/Research and Development/Body design/Body Jigs DXF files/Expeditioner Model-Jig-5.dxf

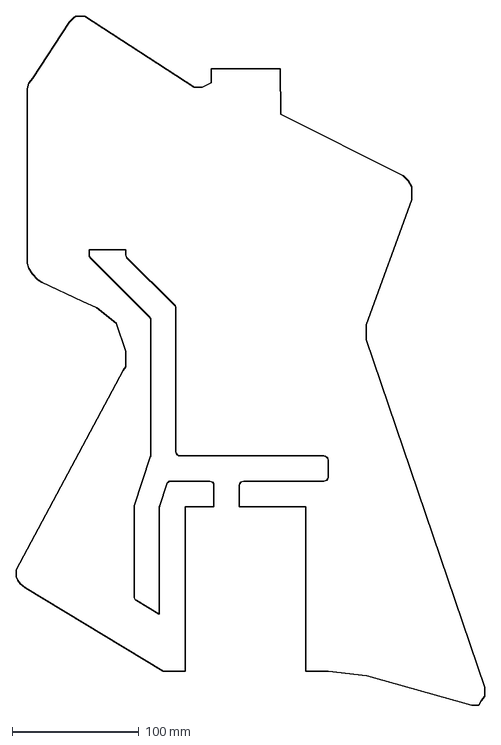
[picture p182: CAD file, 2025-05-16]
Research and Development/Body design/Body Jigs DXF files/Expeditioner Model-Jig-5.dxf
369.2 x 543.6 mm
