Wierdwizard2587/ElectricGuitarMK1/Research and Development/Body design/Expeditioner Model-Guitar Componentssleeve enclosure v2.stl

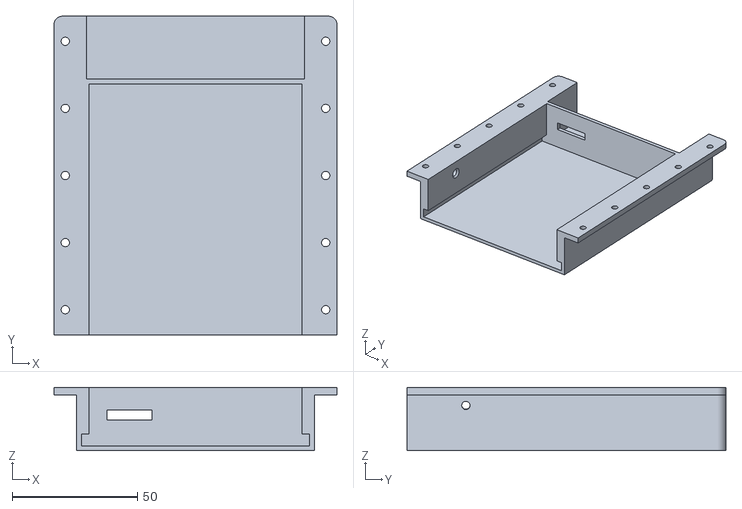
[picture p183: CAD file, 2025-05-16]
Research and Development/Body design/Expeditioner Model-Guitar Componentssleeve enclosure v2.stl
112.8 x 127.0 x 25.3
