Wierdwizard2587/ElectricGuitarMK1/Research and Development/Interface Section/AFPI/Enclosure Design/Top Plate CNC Job.FCStd

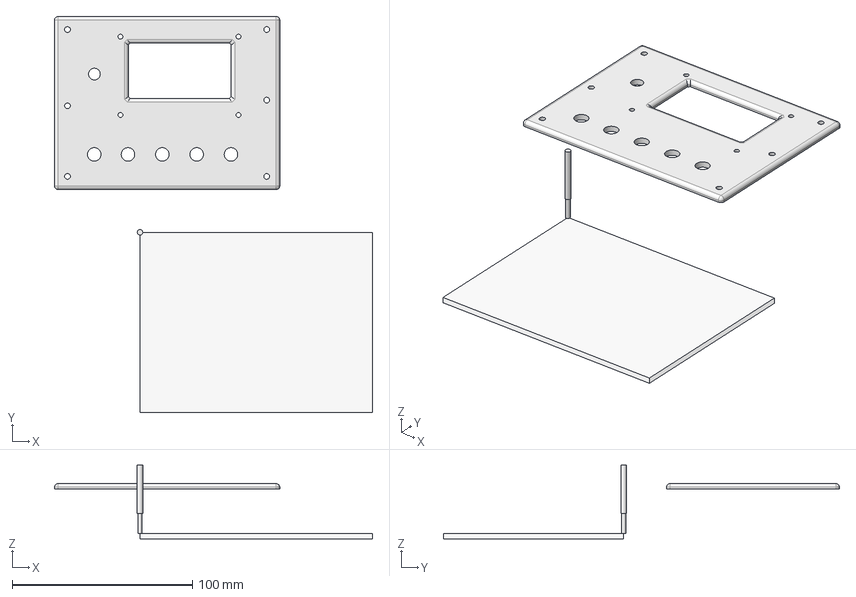
[picture p184: CAD file, 2025-05-16]
Research and Development/Interface Section/AFPI/Enclosure Design/Top Plate CNC Job.FCStd
176.5 x 219.7 x 41.0 mm
Top Plate
Model-Top Enclosure Plate
Endmill
Stock001
