Wierdwizard2587/ElectricGuitarMK1/Research and Development/Storage Draw seperators/storage draw seperator 1.stl

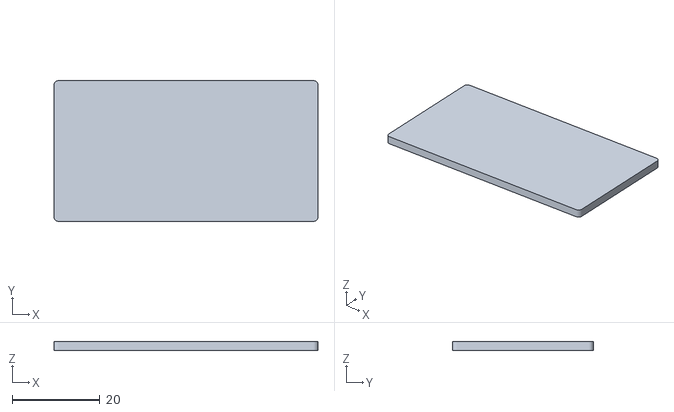
[picture p186: CAD file, 2024-06-03]
Research and Development/Storage Draw seperators/storage draw seperator 1.stl
60.0 x 32.0 x 2.00
