Wierdwizard2587/ElectricGuitarMK1/Research and Development/BMS/enclosure modelling/Battery Cell Mount Designs - not-utilised-Anymore/Battery holder initial designing/2_Batterie_2.0.stl

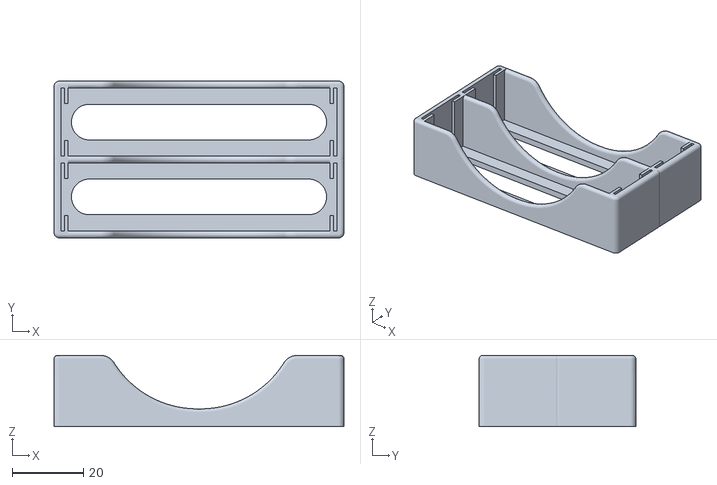
[picture p187: CAD file, 2024-06-03]
Research and Development/BMS/enclosure modelling/Battery Cell Mount Designs - not-utilised-Anymore/Battery holder initial designing/2_Batterie_2.0.stl
81.4 x 44.0 x 20.0
