Wierdwizard2587/ElectricGuitarMK1/Research and Development/BMS/FInal Battery Design/Final Battery Design-batt sleeve v2sleeve enclosure top plate.step

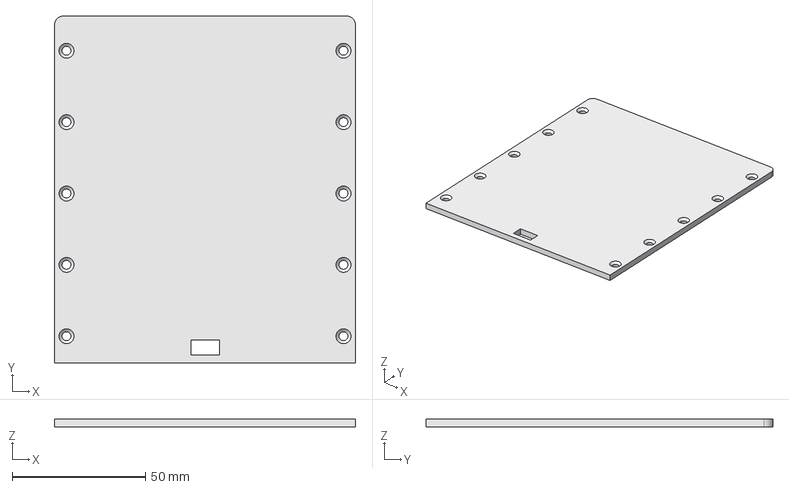
[picture p189: CAD file, 2025-05-16]
Research and Development/BMS/FInal Battery Design/Final Battery Design-batt sleeve v2sleeve enclosure top plate.step
112.8 x 130.0 x 3.00 mm
