Wierdwizard2587/ElectricGuitarMK1/Research and Development/Body design/body Components Tool Paths/AFPI Mounts.FCStd

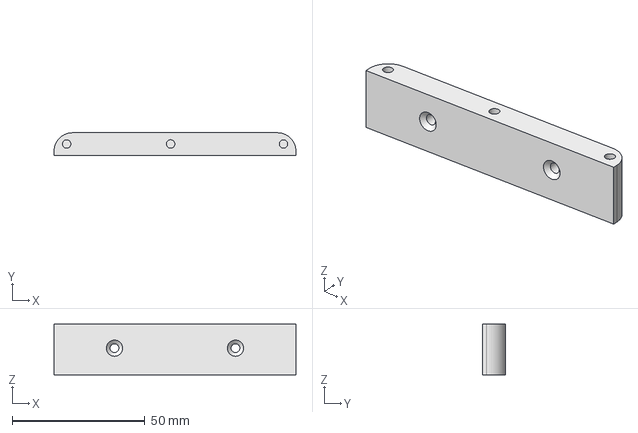
[picture p190: CAD file, 2025-05-16]
Research and Development/Body design/body Components Tool Paths/AFPI Mounts.FCStd
91.0 x 8.50 x 19.0 mm
