Wierdwizard2587/ElectricGuitarMK1/Research and Development/Body design/Expeditioner Model.FCStd

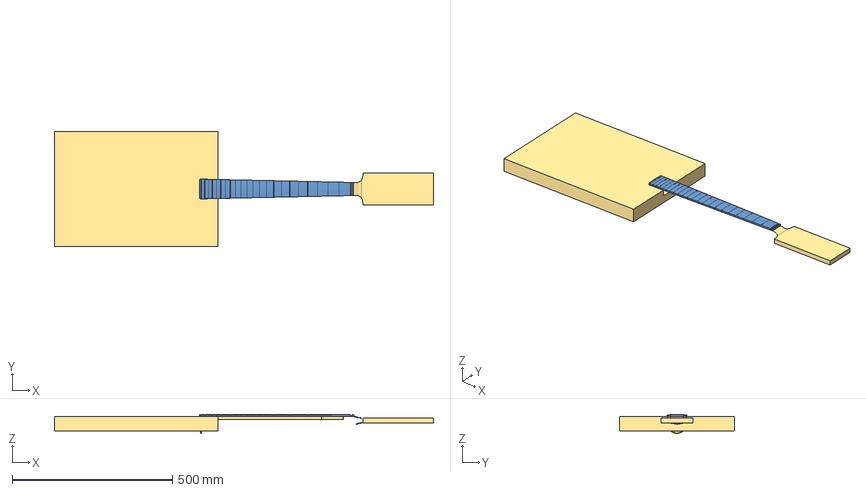
[picture p192: CAD file, 2024-08-25]
Research and Development/Body design/Expeditioner Model.FCStd
1182.3 x 360.0 x 59.3 mm
Fretboard
Neck
Body Back
