Wierdwizard2587/ElectricGuitarMK1/Research and Development/Interface Section/AFPI/Enclosure Design/Acrylic Plating Gcode/Bottom Plate CNC Job.FCStd

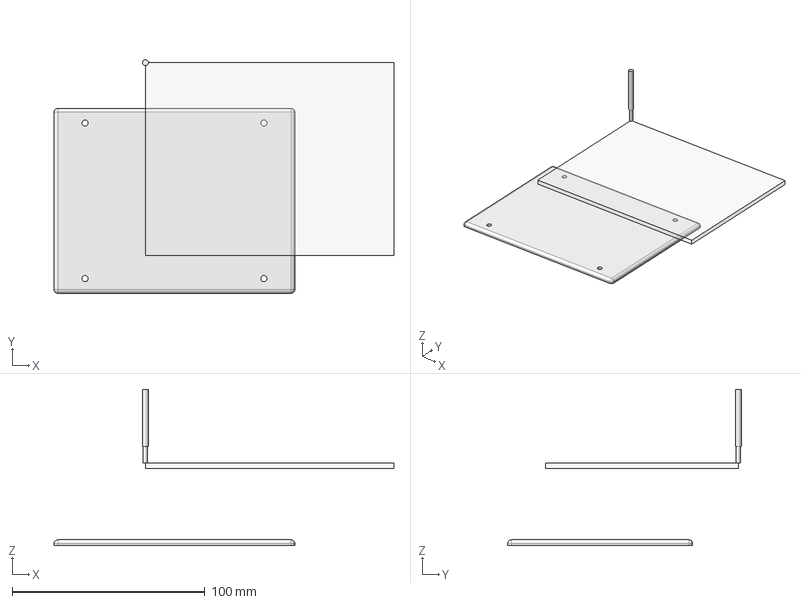
[picture p193: CAD file, 2024-08-15]
Research and Development/Interface Section/AFPI/Enclosure Design/Acrylic Plating Gcode/Bottom Plate CNC Job.FCStd
176.4 x 121.2 x 81.0 mm
Bottom Plate
Stock001
2.3mm_endmill
