Wierdwizard2587/ElectricGuitarMK1/Research and Development/Interface Section/AFPI/Enclosure Design/AFPI Enclosure Model.FCStd

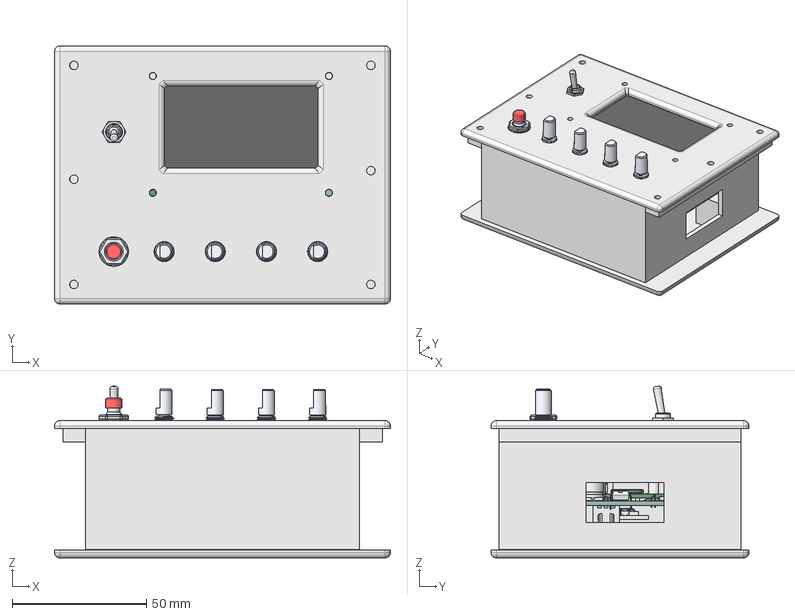
[picture p194: CAD file, 2024-08-15]
Research and Development/Interface Section/AFPI/Enclosure Design/AFPI Enclosure Model.FCStd
125.0 x 96.0 x 63.9 mm
Hole
BMxB-SRSS-TB
BMxB-SRSS-TB001
BMxB-SRSS-TB002
BMxB-SRSS-TB003
BMxB-SRSS-TB004
BMxB-SRSS-TB005
BMxB-SRSS-TB006
BMxB-SRSS-TB008
BMxB-SRSS-TB009
BMxB-SRSS-TB010
BMxB-SRSS-TB011
BMxB-SRSS-TB012
BMxB-SRSS-TB013
BMxB-SRSS-TB014
Washer
Cap
Metal Body
Plastic Body
Contact 1
Contact 2
Nut
_autosave-AFPI Device V1.1 PCB
Top Plate
Enclosure Centre and mounts
left Lip mount
right Lip mount
bottom left pcb mount
top left pcb mount
bottom right pcb mount
Hole011
Hole012
Hole013
Hole014
Hole015
Bottom Plate
