Wierdwizard2587/ElectricGuitarMK1/Research and Development/Interface Section/RGB Lighting comps/RGB LED Mounting Board/RGB Light Case.FCStd

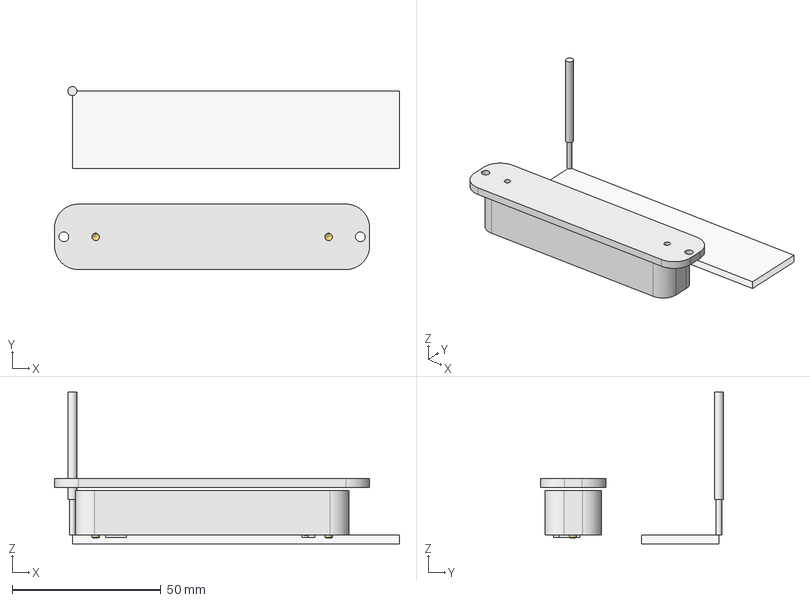
[picture p195: CAD file, 2025-05-16]
Research and Development/Interface Section/RGB Lighting comps/RGB LED Mounting Board/RGB Light Case.FCStd
116.0 x 61.6 x 51.0 mm
lighting case
RGB LED Mounting Board PCB001
M2.5_MF_TORRETTA001
M2.5_MF_TORRETTA
Acrylic Clear Plate001
Stock
2mm_Endmill
