Wierdwizard2587/ElectricGuitarMK1/Research and Development/Storage Draw seperators/paperdraw organisers.FCStd

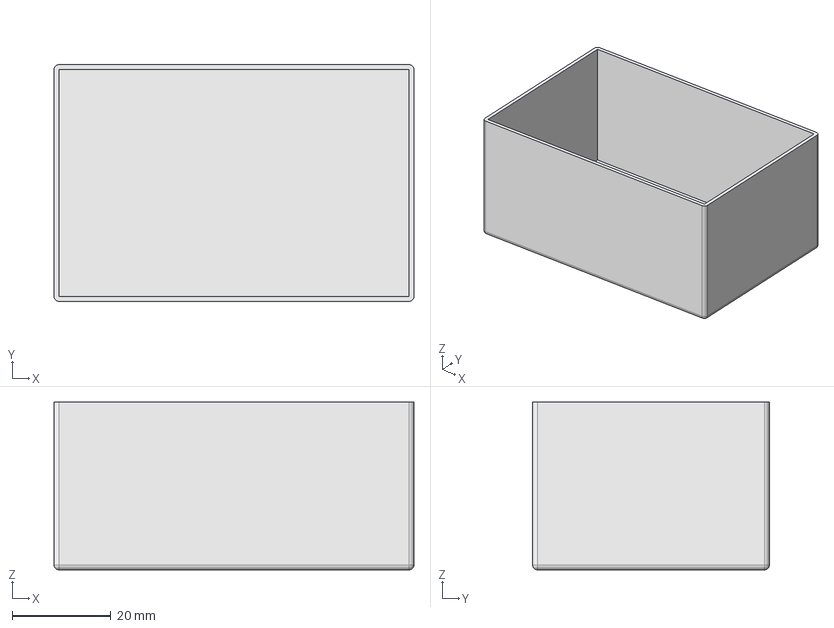
[picture p196: CAD file, 2024-06-03]
Research and Development/Storage Draw seperators/paperdraw organisers.FCStd
73.0 x 48.0 x 34.0 mm
