Wierdwizard2587/ElectricGuitarMK1/Research and Development/Body design/body Components Tool Paths/Back plate 3 tool job.FCStd

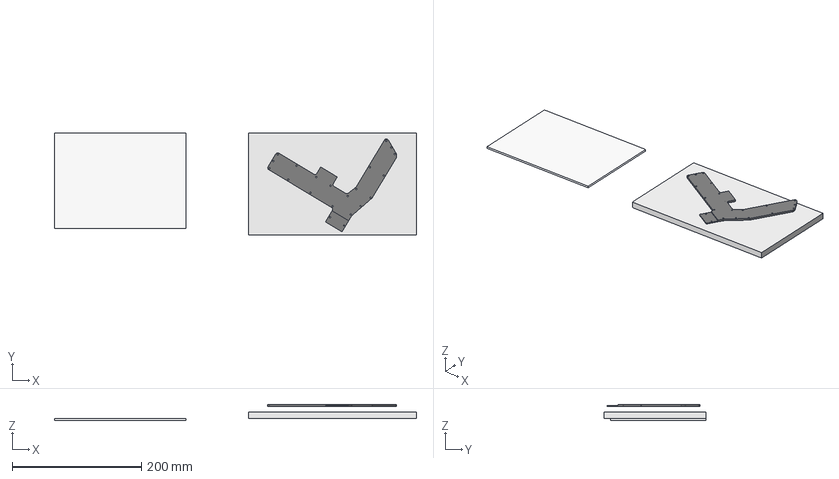
[picture p198: CAD file, 2025-05-16]
Research and Development/Body design/body Components Tool Paths/Back plate 3 tool job.FCStd
560.0 x 158.0 x 25.0 mm
Back Plate 3
Stock001
