Wierdwizard2587/ElectricGuitarMK1/Research and Development/BMS/FInal Battery Design/battery mount section test 1.step

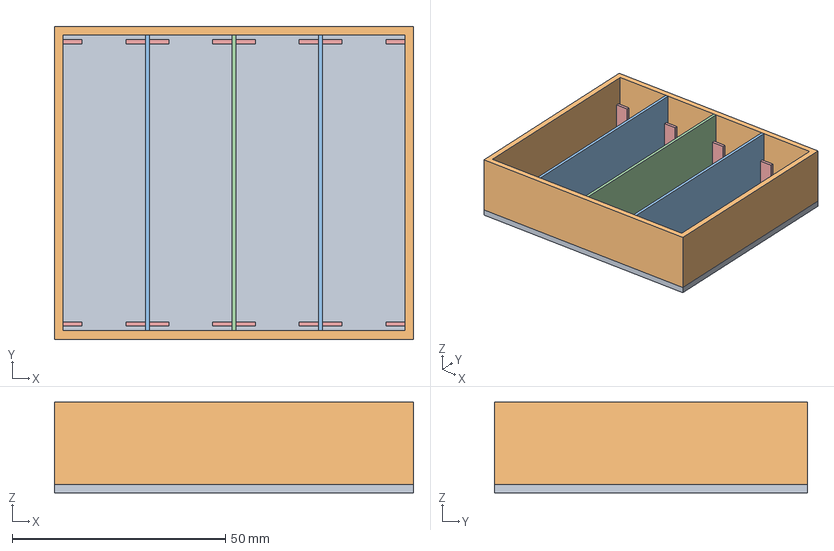
[picture p201: CAD file, 2024-09-18]
Research and Development/BMS/FInal Battery Design/battery mount section test 1.step
84.2 x 73.3 x 21.3 mm
Sketch004
Sketch005
