Wierdwizard2587/ElectricGuitarMK1/Research and Development/Body design/Body Jigs DXF files/Expeditioner Model-Jig-1.dxf

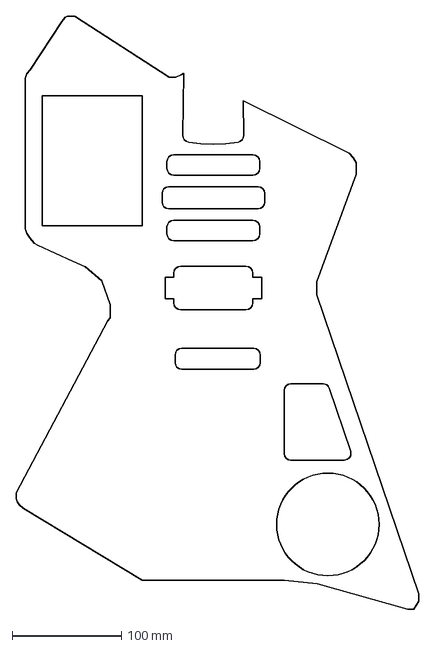
[picture p202: CAD file, 2025-05-16]
Research and Development/Body design/Body Jigs DXF files/Expeditioner Model-Jig-1.dxf
369.2 x 543.6 mm
