Wierdwizard2587/ElectricGuitarMK1/Research and Development/BMS/enclosure modelling/Battery Cell Mount Designs - not-utilised-Anymore/Battery holder initial designing/original battery holder measurements.FCStd

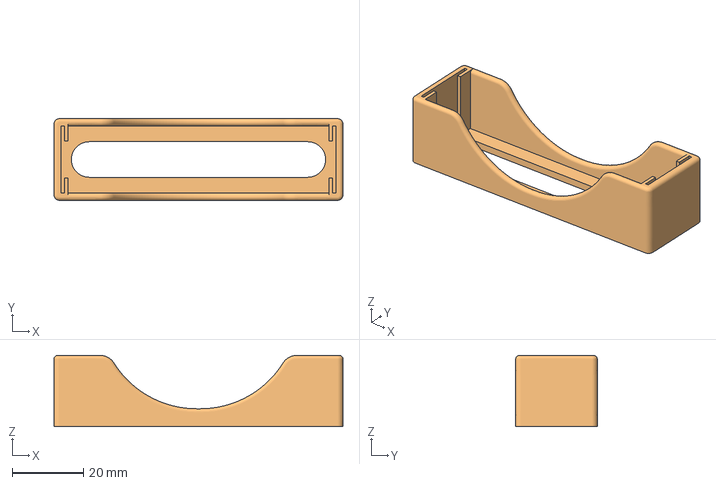
[picture p203: CAD file, 2024-06-03]
Research and Development/BMS/enclosure modelling/Battery Cell Mount Designs - not-utilised-Anymore/Battery holder initial designing/original battery holder measurements.FCStd
81.4 x 23.0 x 20.0 mm
__Batterie_2_001
1_Batterie_2.0
