Wierdwizard2587/ElectricGuitarMK1/Research and Development/BMS/enclosure modelling/Battery Cell Mount Designs - not-utilised-Anymore/Design attempt 2 - final/battery design reexport 3.stl

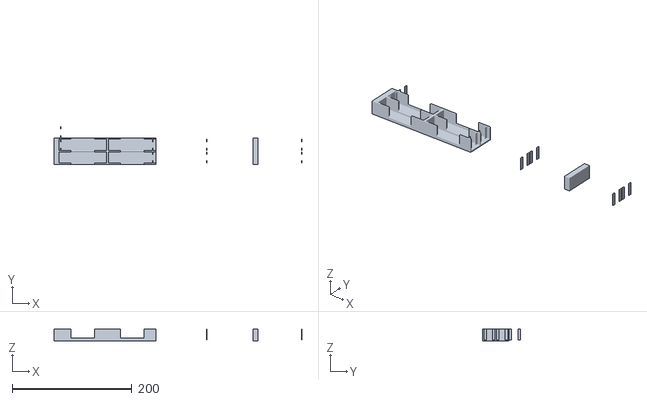
[picture p204: CAD file, 2024-06-03]
Research and Development/BMS/enclosure modelling/Battery Cell Mount Designs - not-utilised-Anymore/Design attempt 2 - final/battery design reexport 3.stl
414.5 x 63.0 x 20.0
