Wierdwizard2587/ElectricGuitarMK1/Research and Development/Storage Draw seperators/paperdraw organiser1.stl

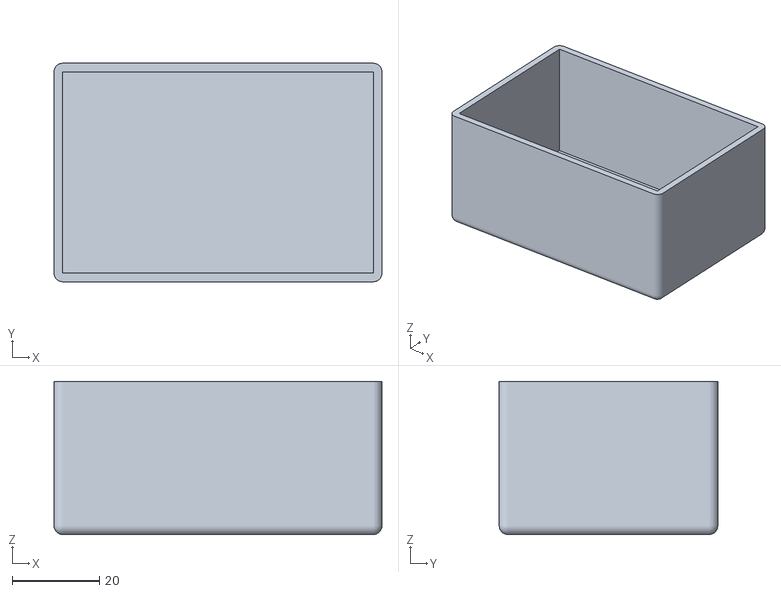
[picture p205: CAD file, 2024-06-03]
Research and Development/Storage Draw seperators/paperdraw organiser1.stl
75.0 x 50.0 x 35.0
