Wierdwizard2587/ElectricGuitarMK1/Research and Development/BMS/enclosure modelling/Battery Cell Mount Designs - not-utilised-Anymore/Design attempt 2 - final/battery top row 1.stl

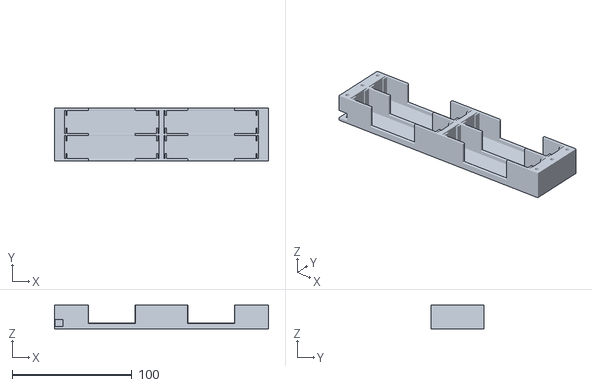
[picture p206: CAD file, 2024-06-03]
Research and Development/BMS/enclosure modelling/Battery Cell Mount Designs - not-utilised-Anymore/Design attempt 2 - final/battery top row 1.stl
179.0 x 44.0 x 20.0
