Wierdwizard2587/ElectricGuitarMK1/Progress Photos/MK 0 attempt/Mk0 wiring.png

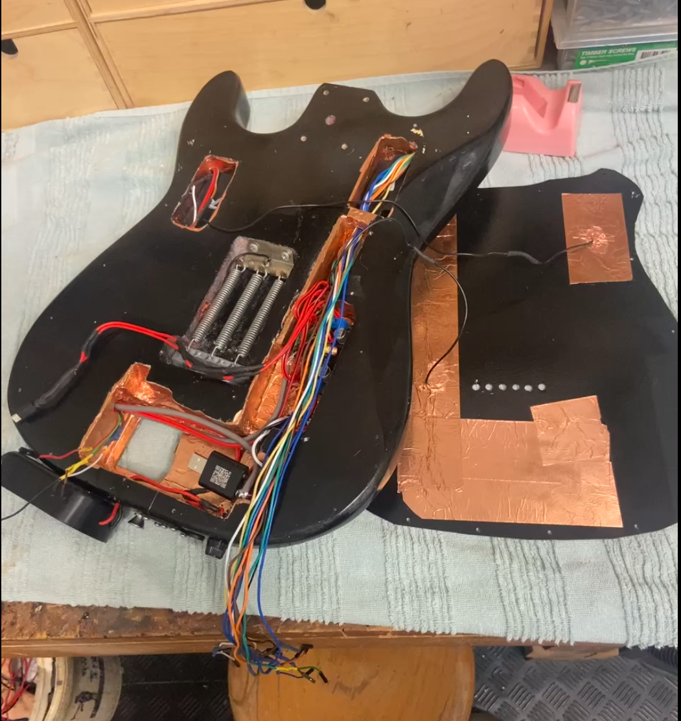
Progress Photos/MK 0 attempt/Mk0 wiring.png
