Wierdwizard2587/ElectricGuitarMK1/Research and Development/BMS/PCB Design/1.0 BMS/comparator setup before alteration.png

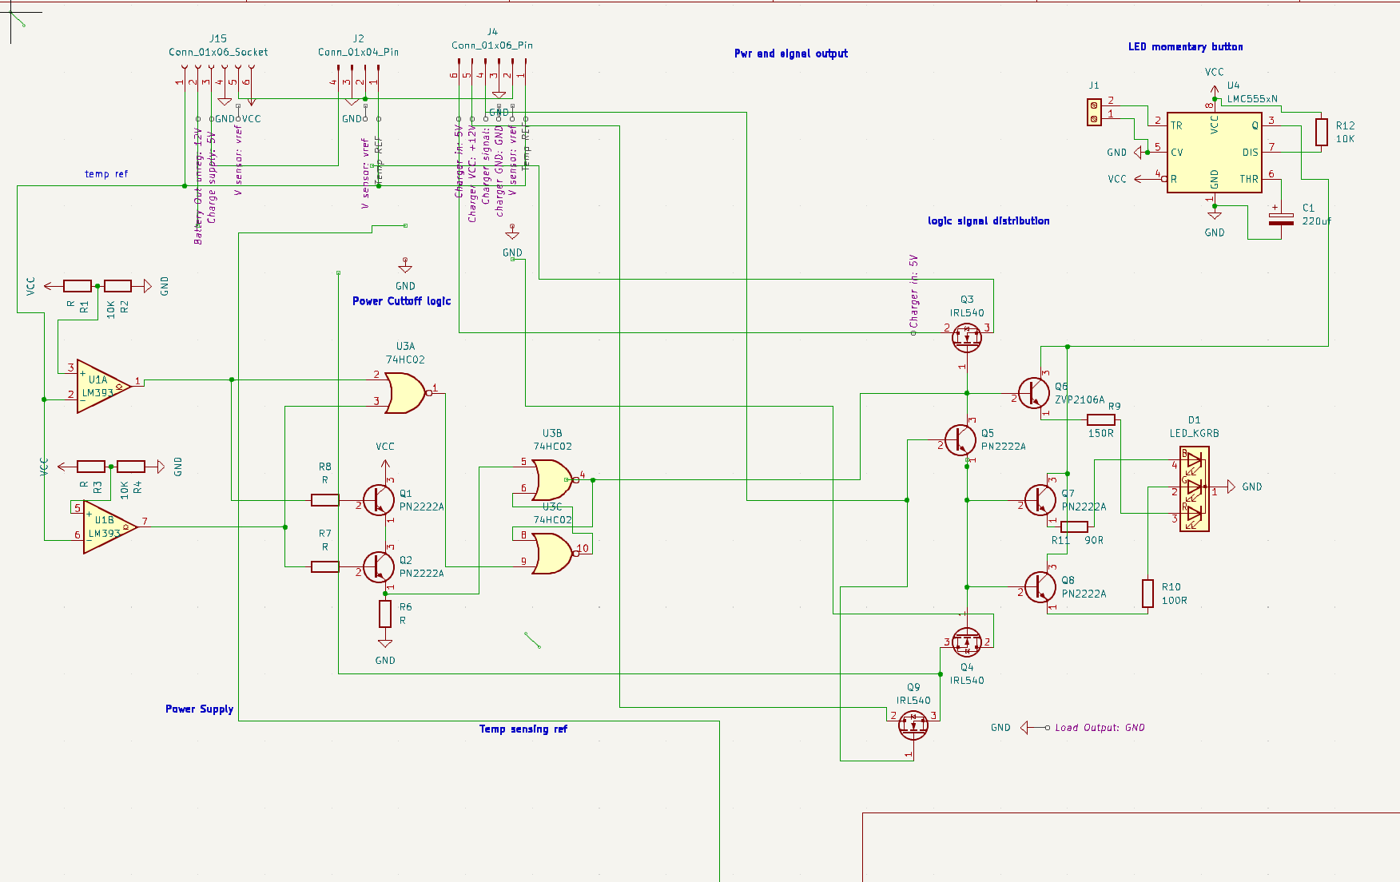
Research and Development/BMS/PCB Design/1.0 BMS/comparator setup before alteration.png
