Wierdwizard2587/ElectricGuitarMK1/Research and Development/BMS/PCB Design/3.0 BMS/V3.1/BMS MK2 attempt 1-using-Tp4506.kicad_pcb

## KiCad design Research and Development/BMS/PCB Design/3.0 BMS/V3.1/BMS MK2 attempt 1-using-Tp4506.kicad_pcb (2024-06-01, an earlier design)

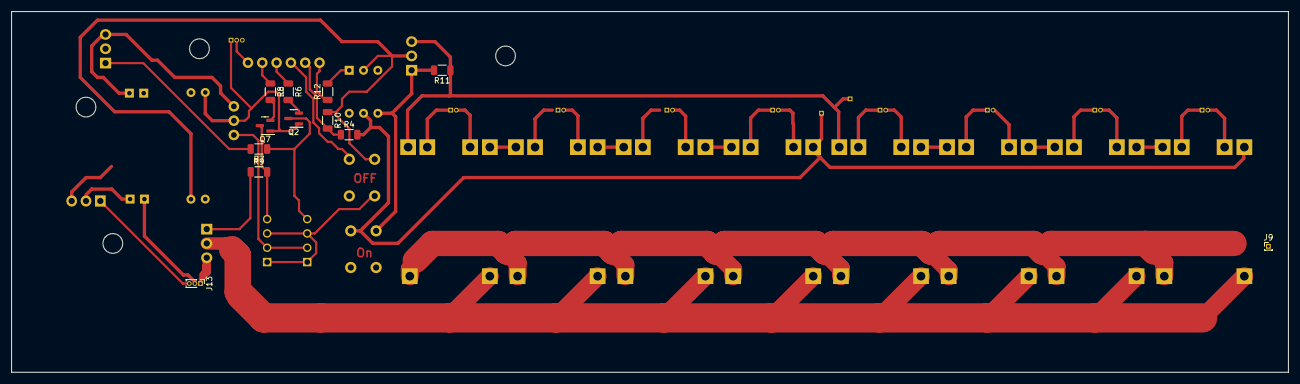
[picture p243: board BMS MK2 attempt 1-using-Tp4506.kicad_pcb from above]

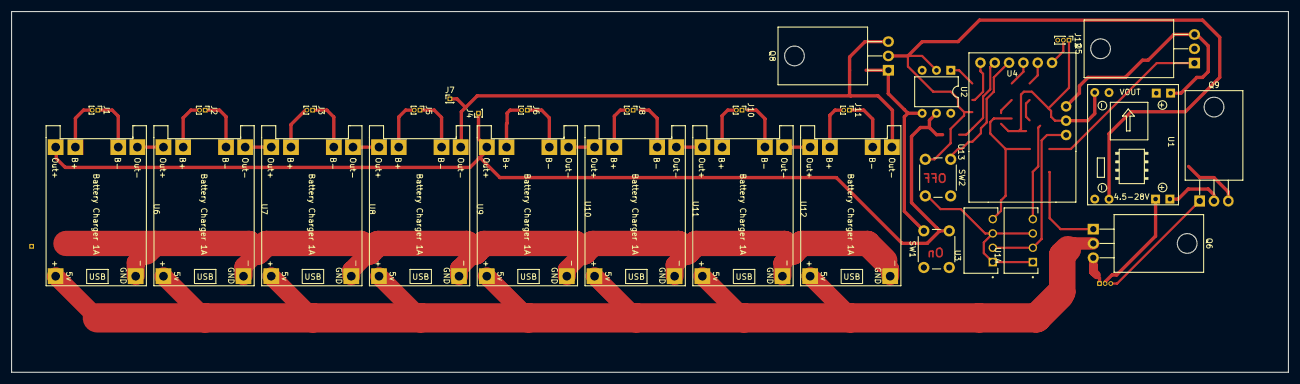
[picture p244: board BMS MK2 attempt 1-using-Tp4506.kicad_pcb from below]

Board: 2 copper layers, 226.6 x 64.0 mm, 42 parts (30 on the bottom side), 45 nets.

Parts:
J1: Batt 1 Conn; PinHeader_1x02_P1.00mm_Vertical
J2: Batt 2 Conn; PinHeader_1x02_P1.00mm_Vertical
J3: Batt 3 Conn; PinHeader_1x02_P1.00mm_Vertical
J4: Battery + out; PinHeader_1x01_P1.00mm_Vertical
J5: Batt 4 Conn; PinHeader_1x02_P1.00mm_Vertical
J6: Batt 5 Conn; PinHeader_1x02_P1.00mm_Vertical
J7: Battery - out; PinHeader_1x01_P1.00mm_Vertical
J8: Batt 6 Conn; PinHeader_1x02_P1.00mm_Vertical
J9: CHG GND; PinHeader_1x01_P1.00mm_Vertical
J10: Batt 7 Conn; PinHeader_1x02_P1.00mm_Vertical
J11: Batt 8 Conn; PinHeader_1x02_P1.00mm_Vertical
J12: Conn_01x03_Pin; PinHeader_1x03_P1.00mm_Vertical
J13: CHG VCCs; PinHeader_1x03_P1.00mm_Vertical
Q2, Q7: PN100; SOT-23
Q5, Q6, Q9: IRF9540N; TO-220-3_Horizontal_TabDown
Q8: IRF540N; TO-220-3_Horizontal_TabDown
R4, R7, R9, R10: 10K; R_1206_3216Metric
R6, R8: 3k3; R_1206_3216Metric
R11: 100K; R_1206_3216Metric
R12: 430R; R_1206_3216Metric
SW1, SW2: SW_SPST; SW_PUSH_6mm
U1: MP1584; SRT_MPT1584EN_Module
U2: 4N35; DIP-6_W7.62mm
U3, U14: B0515S; CONV_B0515S-1WR3
U4: ATTiny 85 Module; Digispark attiny85 board
U6, U7, U8, U9, U10, U11, U12, U13: TP4056 Charging Module; TP4056-18650

Connections:
5v attiny out: J12.3, U3.2 (Vin), U4.1 (5V), U14.2 (Vin)
15v+ CHG VCC: Q7.3 (C), R9.2, U14.4 (+Vo)
15v+ DCHG VCC: Q2.3 (C), R7.1, U3.4 (+Vo)
Batt +: J4.1, Q9.3 (S), R4.2, SW1.2 (B), U2.5, U6.3 (OUT+), U10.3 (OUT+)
Batt -: J7.1, Q8.3 (S), R11.1, U9.4 (OUT-), U13.4 (OUT-)
Batt SW VCC: R12.1, U4.9 (P5)
Battery Vref: R4.1, R10.2, U4.8 (P4)
CGE SW VCC: Q6.1 (G), R9.1
Charge VCC: Q6.2 (D), U6.1 (IN+), U7.1 (IN+), U8.1 (IN+), U9.1 (IN+), U10.1 (IN+), U11.1 (IN+), U12.1 (IN+), U13.1 (IN+)
Chgr CHG 5V+: J13.1, Q6.3 (S)
Chgr operating 12V+: J13.2, Q9.2 (D), U1.1 (IN+)
Chgr sgl 15V+: J13.3, Q9.1 (G)
DCG SW VCC: Q5.1 (G), R7.2
GND: J12.1, Q2.1 (E), Q7.1 (E), Q8.2 (D), R10.1, SW2.2 (B), U1.2 (IN-), U1.4 (OUT-), U2.2, U3.1 (GND), U3.3 (0V), U4.2 (GND), U6.2 (IN-), U7.2 (IN-), U8.2 (IN-), U9.2 (IN-), U10.2 (IN-), U11.2 (IN-), U12.2 (IN-), U13.2 (IN-), U14.1 (GND), U14.3 (0V)
unnamed: J1.1, U6.6 (B-)
unnamed: J1.2, U6.5 (B+)
unnamed: J2.1, U7.6 (B-)
unnamed: J2.2, U7.5 (B+)
unnamed: J3.1, U8.6 (B-)
unnamed: J3.2, U8.5 (B+)
unnamed: J5.1, U9.6 (B-)
unnamed: J5.2, U9.5 (B+)
unnamed: J6.1, U10.6 (B-)
unnamed: J6.2, U10.5 (B+)
unnamed: J8.1, U11.6 (B-)
unnamed: J8.2, U11.5 (B+)
unnamed: J10.1, U12.6 (B-)
unnamed: J10.2, U12.5 (B+)
unnamed: J11.1, U13.6 (B-)
unnamed: J11.2, U13.5 (B+)
unnamed: J12.2, U4.4 (P0)
unnamed: Q2.2 (B), R6.2
unnamed: Q7.2 (B), R8.2
unnamed: Q8.1 (G), R11.2, SW1.1 (A), U2.4
unnamed: R12.2, U2.1
unnamed: SW2.1 (A), U4.7 (P3)
unnamed: R8.1, U4.5 (P1)
unnamed: R6.1, U4.6 (P2)
unnamed: U6.4 (OUT-), U7.3 (OUT+)
unnamed: U7.4 (OUT-), U8.3 (OUT+)
unnamed: U8.4 (OUT-), U9.3 (OUT+)
unnamed: U10.4 (OUT-), U11.3 (OUT+)
unnamed: U11.4 (OUT-), U12.3 (OUT+)
unnamed: U12.4 (OUT-), U13.3 (OUT+)
Reg Batt 9v: Q5.3 (S), U1.3 (OUT+), U4.3 (VIN)
