Wierdwizard2587/ElectricGuitarMK1/Research and Development/BMS/FInal Battery Design/Battery final Rev/Battery final Rev.kicad_sch

## KiCad design Research and Development/BMS/FInal Battery Design/Battery final Rev/Battery final Rev.kicad_sch (2024-09-18)

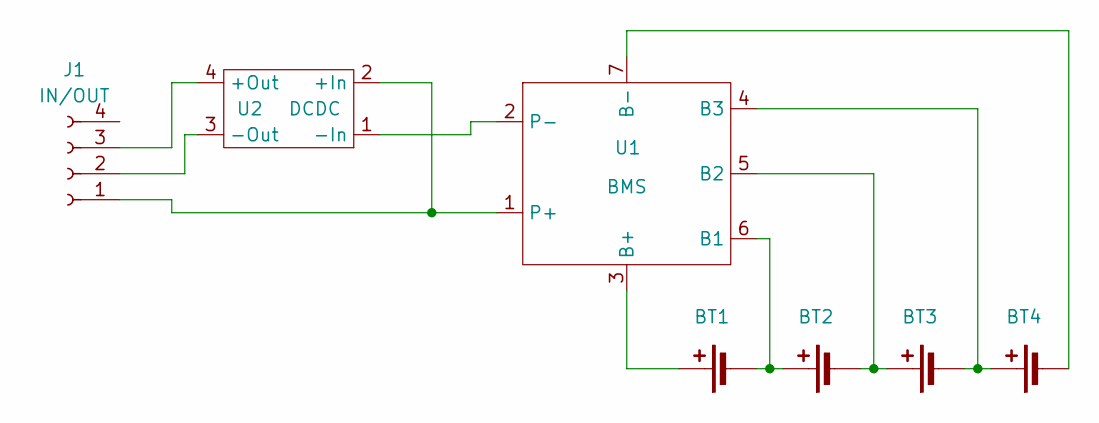
[picture p245: schematic Battery final Rev.kicad_sch]

Parts:
BT1, BT2, BT3, BT4: Battery_Cell
J1: IN/OUT
U1: BMS
U2: DCDC

Connections:
unnamed: BT1.1 (+), U1.3 (B+)
unnamed: BT1.2 (-), BT2.1 (+), U1.6 (B1)
unnamed: BT2.2 (-), BT3.1 (+), U1.5 (B2)
unnamed: BT3.2 (-), BT4.1 (+), U1.4 (B3)
unnamed: BT4.2 (-), U1.7 (B-)
unnamed: J1.1, U1.1 (P+), U2.2 (+In)
unnamed: J1.2, U2.3 (-Out)
unnamed: J1.3, U2.4 (+Out)
unnamed: U1.2 (P-), U2.1 (-In)
