Wierdwizard2587/ElectricGuitarMK1/Research and Development/Interface Section/AFPI/Firmware/MainV1.1/aux_pages.cpp

#include "aux_pages.h"


#include "config.h"
#include "audio_processing.h"
#include "rotary_encoder_ctrl.h"
#include "display.h"
#include "home_button.h"
#include "RGB_processing.h"

float vol;
int gain;

void masterAuxPage() {
  while (!ss.digitalRead(SS_ENC3_SWITCH)) {
    delay(50);
  }
  currentAuxPage = 0;

  while (true) {

    if (currentAudioOutput == 0){
      vol = SPVol;
      gain = SPGainOut;

    }
    if (currentAudioOutput == 1){
      vol = HPVol;
      gain = HPGainOut;
    }
    if (currentAudioOutput == 2){
      vol = AUXVol;
      gain = AuxGainOut;
    }

    char title[] = {"Aux #1 Master Vol"};
    bool notFX = false;
    setFXTemplatePage(title, notFX, false);
    display.setCursor(1, 20);
    display.print("MasVol:");
    display.setCursor(10, 35);
    display.println(vol);
    display.setCursor(55, 20);
    display.print("Gain:");
    display.setCursor(60, 35);
    display.println(gain);
    display.setCursor(80, 20);
    display.print("Out:");
    display.setCursor(90, 35);
    display.println(currentAudioOutput);
    display.display();


    checkRGBinterval();

    checkScreenTime();
    
    checkHomeButton();

    //Master volume Control Encoder Check
    int EncRes;
    EncRes = EncDialCheck(0, vol, 1.0, 0.0);
    if (EncRes == 2) {
      vol = vol + 0.05;
      determineOutputVol(vol);
    } 
    if (EncRes == 1) {
      vol = vol - 0.05;
      determineOutputVol(vol);
      //audioShield.volume(masterVolume);
    }
    //Master Gain out Control Encoder Check
    EncRes = EncDialCheck(1, gain, 31, 13);
    if (EncRes == 2) {
      gain = gain + 1;
      determineOutputGain(gain);
    } 
    if (EncRes == 1) {
      gain = gain - 1;
      determineOutputGain(gain);
      //audioShield.lineOutLevel(gainOut);
    }
    //audioShield.dacVolume(0.0, 0.0);
    //audio output selection, 0 = speaker, 1 = headphones, 2 = aux out
    if (!ss.digitalRead(SS_ENC3_SWITCH)) {
      if (currentAudioOutput == 2){ //switch to speaker, next change will be hp
          currentAudioOutput = 0;

          audioShield.lineOutLevel(SPGainOut, 31);
          audioShield.dacVolume(SPVol, 0.05);

      } else if (currentAudioOutput == 0){ // switch to hp, next change will be aux out
          currentAudioOutput = 1;
          audioShield.unmuteHeadphone();
          audioShield.muteLineout();

          audioShield.dacVolume(1.0, 1.0);
          
          audioShield.volume(HPVol);
          audioShield.lineOutLevel(HPGainOut);

      } else if (currentAudioOutput == 1){ // switch to aux out, next change will be speaker
          currentAudioOutput = 2;
          audioShield.muteHeadphone();
          audioShield.unmuteLineout();
          //audioShield.lineOutLevel(31, 13);
          audioShield.dacVolume(0.05, AUXVol);
          audioShield.lineOutLevel(31, AuxGainOut);
      }
    }

    while (!ss.digitalRead(SS_ENC3_SWITCH)) {
    delay(50);
    }


    cycleAux(3, currentAuxPage, 1.0, 0.0);//Check FX selected change 
    
  }
}


void determineOutputVol(float selVol) {
  if (currentAudioOutput == 0){
    audioShield.dacVolume(selVol, 0.05);
    SPVol = selVol;
  }
  if (currentAudioOutput == 1){
    audioShield.volume(selVol);
    HPVol = selVol;
  }
  if (currentAudioOutput == 2){
    audioShield.dacVolume(0.05, selVol);
    AUXVol = selVol;
  }
}

void determineOutputGain(int selGain) {
  if (currentAudioOutput == 0){
    audioShield.lineOutLevel(selGain, 31);
    SPGainOut = selGain;

  }
  if (currentAudioOutput == 1){
    audioShield.lineOutLevel(selGain);
    HPGainOut = selGain;
  }
  if (currentAudioOutput == 2){
    audioShield.lineOutLevel(31, selGain);
    AuxGainOut = selGain;
  }
}



void backTrackAuxPage() {
  while (!ss.digitalRead(SS_ENC3_SWITCH)) {
    delay(50);
  }
  currentAuxPage = 1;
  while (true) {
    char title[] = {"Aux #2 Back Track"};
    bool notFX = false;
    setFXTemplatePage(title, notFX, false);
    display.setCursor(1, 20);
    display.print("Line Mx:");
    display.setCursor(10, 35);
    display.println(lineMix);
    display.setCursor(55, 20);
    display.print("Back Mx:");
    display.setCursor(60, 35);
    display.println(backingMix);
    display.display();

    checkRGBinterval();
    checkScreenTime();
    checkHomeButton();

    //Master volume Control Encoder Check
    int EncRes;
    param = lineMix;
    EncRes = EncDialCheck(0, param, 3.0, 0.0);
    if (EncRes == 2) {
      lineMix = lineMix + 0.05;
      master_mix.gain(1, lineMix);
    } 
    if (EncRes == 1) {
      lineMix = lineMix - 0.05;
      master_mix.gain(1, lineMix);
    }
    //Master Gain out Control Encoder Check
    param = backingMix;
    EncRes = EncDialCheck(1, param, 3.0, 0.0);
    if (EncRes == 2) {
      backingMix = backingMix + 0.05;
      master_mix.gain(0, backingMix);
    } 
    if (EncRes == 1) {
      backingMix = backingMix - 0.05;
      master_mix.gain(0, backingMix);
    }

    cycleAux(3, currentAuxPage, 1.0, 0.0);//Check Aux selected change 
    
  }
}
typedef void (*FunctionPointer)();
FunctionPointer auxFunctions[] = { masterAuxPage, backTrackAuxPage  };

void audioPage() {
    while (!ss.digitalRead(SS_ENC3_SWITCH)) {
    // Debounce delay
    delay(50);
  }
  auxFunctions[currentAuxPage]();;
}

void cycleAux(int encNo, int param, int maxRange, int minRange) {
    int EncRes;
    EncRes = EncDialCheck(encNo, param, maxRange, minRange);
    if (EncRes == 2) {
        auxFunctions[param + 1]();;
    } 
    if (EncRes == 1) {
        auxFunctions[param - 1]();;
    }  
}
