Wierdwizard2587/ElectricGuitarMK1/Research and Development/Interface Section/AFPI/Firmware/MainV1.1/aux_pages.h

#ifndef AUX_PAGES_H
#define AUX_PAGES_H


#include "config.h"
#include "rotary_encoder_ctrl.h"
#include "display.h"

void masterAuxPage();
void backTrackAuxPage();

typedef void (*FunctionPointer)();
extern FunctionPointer auxFunctions[];

void audioPage();
void cycleAux(int encNo, int param, int maxRange, int minRange);

extern float vol;
extern int gain;
void determineOutputGain(int selGain);
void determineOutputVol(float selVol);
#endif
