Wierdwizard2587/ElectricGuitarMK1/Research and Development/Interface Section/AFPI/Firmware/MainV1.1/home_button.h

#ifndef HOME_BUTTON_H
#define HOME_BUTTON_H

#include "config.h"
#include "landing_page.h"
//#include "SD_card.h"
extern const int buttonPin;

void checkHomeButton();
bool homeButtonActivity();
#endif
