Wierdwizard2587/ElectricGuitarMK1/Research and Development/Interface Section/AFPI/Firmware/MainV1.1/FX_pages.h

#ifndef FX_PAGES_H
#define FX_PAGES_H


#include "config.h"
#include "rotary_encoder_ctrl.h"
#include "display.h"

void flangeFX();
void chorusFX();
void reverbFX();
void delayFX();
void cycleFX(int encNo, int param, int maxRange, int minRange);
void FXMainPage();

#endif
