Wierdwizard2587/ElectricGuitarMK1/Research and Development/Interface Section/Teensy Test Scripts/quad rotary encoder adafruit board/rotaryencoderAudioBoardComboTest/rotaryencoderAudioBoardComboTest.ino

/*
 * This is a demo for a Teensy 4.0 connected to a quad rotary encoder breakout
 * using the onboard I2C pins
 * https://www.adafruit.com/product/4900
 * https://www.adafruit.com/product/5752
 * 
 */
#include "Adafruit_seesaw.h"
#include <seesaw_neopixel.h>

#define SS_NEO_PIN       18
#define SS_ENC0_SWITCH   12
#define SS_ENC1_SWITCH   14
#define SS_ENC2_SWITCH   17
#define SS_ENC3_SWITCH   9

#define SEESAW_ADDR      0x49


#include <Audio.h>
#include <Wire.h>
#include <SPI.h>
#include <SD.h>
#include <SerialFlash.h>

// GUItool: begin automatically generated code
AudioInputI2S            i2s1_in;           //xy=466.11112213134766,339.28570556640625

AudioEffectFreeverb      freeverb;      //xy=743.857177734375,336.8571472167969

AudioOutputI2S           i2s2_out;           //xy=923.888916015625,332.8888854980469



AudioConnection          patchCord1(i2s1_in, 0, freeverb, 0);
AudioConnection          patchCord2(freeverb, 0, i2s2_out, 0);
AudioConnection          patchCord3(freeverb, 0, i2s2_out, 1);

AudioControlSGTL5000     audioShield;     //xy=862.3333740234375,235.2222442626953
// GUItool: end automatically generated code

const int inputChSelect = AUDIO_INPUT_LINEIN;

// audio shield volume
int masterVolume = 0;

float roomsizeamt = 0.5;

float dampingamt = 0.5;



Adafruit_seesaw ss = Adafruit_seesaw(&Wire1);
seesaw_NeoPixel pixels = seesaw_NeoPixel(4, SS_NEO_PIN, NEO_GRB + NEO_KHZ800, &Wire1);

int32_t enc_positions[4] = {0, 0, 0, 0};

void setup() {
    // put your setup code here, to run once:

  
  // Audio connections require memory to work.  For more
  // detailed information, see the MemoryAndCpuUsage example
  AudioMemory(8);

  // Comment these out if not using the audio adaptor board.
  Serial.print("init audio shield...");
  audioShield.enable();
  audioShield.inputSelect(inputChSelect);  // select mic or line-in for audio shield input source
  audioShield.volume(0.5);
  Serial.println("done.");

  freeverb.roomsize(roomsizeamt);
  freeverb.damping(dampingamt);


  Serial.begin(115200);
  while (!Serial) delay(10);

  // Initialize I2C communication
  Wire1.begin();  // No need to specify SDA and SCL pins for Teensy 4.0

  Serial.println("Looking for seesaw!");
  
  if (! ss.begin(SEESAW_ADDR) || !pixels.begin(SEESAW_ADDR)) {
    Serial.println("Couldn't find seesaw on default address");
    while(1) delay(10);
  }
  Serial.println("seesaw started");
  uint32_t version = ((ss.getVersion() >> 16) & 0xFFFF);
  if (version  != 5752){
    Serial.print("Wrong firmware loaded? ");
    Serial.println(version);
    while(1) delay(10);
  }
  Serial.println("Found Product 5752");

  ss.pinMode(SS_ENC0_SWITCH, INPUT_PULLUP);
  ss.pinMode(SS_ENC1_SWITCH, INPUT_PULLUP);
  ss.pinMode(SS_ENC2_SWITCH, INPUT_PULLUP);
  ss.pinMode(SS_ENC3_SWITCH, INPUT_PULLUP);
  ss.setGPIOInterrupts(1UL << SS_ENC0_SWITCH | 1UL << SS_ENC1_SWITCH | 
                       1UL << SS_ENC2_SWITCH | 1UL << SS_ENC3_SWITCH, 1);

  
  // get starting positions
  for (int e=0; e<4; e++) {
    enc_positions[e] = ss.getEncoderPosition(e);
    ss.enableEncoderInterrupt(e);
  }
  
  Serial.println("Turning on interrupts");

  pixels.setBrightness(255);
  pixels.show(); // Initialize all pixels to 'off'
}

void loop() {
  
  if (! ss.digitalRead(SS_ENC0_SWITCH)) {
    Serial.println("ENC0 pressed!");
  }
  if (! ss.digitalRead(SS_ENC1_SWITCH)) {
    Serial.println("ENC1 pressed!");
  }
  if (! ss.digitalRead(SS_ENC2_SWITCH)) {
    Serial.println("ENC2 pressed!");
  }
  if (! ss.digitalRead(SS_ENC3_SWITCH)) {
    Serial.println("ENC3 pressed!");
  }


  int32_t enc_0_pos = ss.getEncoderPosition(0);
  if (enc_positions[0] != enc_0_pos) {
    Serial.print("Encoder #");
    Serial.print(0);
    Serial.print(" -> ");
    Serial.println(enc_0_pos);      // display new position
    enc_positions[0] = enc_0_pos;

    pixels.setPixelColor(0, Wheel((enc_0_pos*4) & 0xFF));
    pixels.show();

    float enc_0_float;
    enc_0_float = static_cast<float>(enc_0_pos);
    enc_0_float = enc_0_float / 20;
    float new_enc_0_value = roomsizeamt + enc_0_float;
    if (new_enc_0_value != 1.00 || new_enc_0_value != 0.00) {

      freeverb.roomsize(new_enc_0_value);
      Serial.print("room Size amount: ");
      Serial.print(new_enc_0_value);
    }
    
  }

  //for (int e=0; e<4; e++) {
    //int32_t new_enc_position = ss.getEncoderPosition(e);
    // did we move around?
    //if (enc_positions[e] != new_enc_position) {
      //Serial.print("Encoder #");
      //Serial.print(e);
      //Serial.print(" -> ");
      //Serial.println(new_enc_position);      // display new position
      //enc_positions[e] = new_enc_position;      // and save for next round
      
      // change the neopixel color, multiply the new position by 4 to speed it up
      //pixels.setPixelColor(e, Wheel((new_enc_position*4) & 0xFF));
      //pixels.show();
    //}
  //}

  // don't overwhelm serial port
  delay(10);
}


uint32_t Wheel(byte WheelPos) {
  WheelPos = 255 - WheelPos;
  if (WheelPos < 85) {
    return seesaw_NeoPixel::Color(255 - WheelPos * 3, 0, WheelPos * 3);
  }
  if (WheelPos < 170) {
    WheelPos -= 85;
    return seesaw_NeoPixel::Color(0, WheelPos * 3, 255 - WheelPos * 3);
  }
  WheelPos -= 170;
  return seesaw_NeoPixel::Color(WheelPos * 3, 255 - WheelPos * 3, 0);
}
